JCam98/me210-engineering-design-graphics/Assignments/Reverse Engineering Project/Design Checks/Design_Check_4/PDFS/PART_1_PLASTIC_CASE.pdf

## PLASTIC CASE

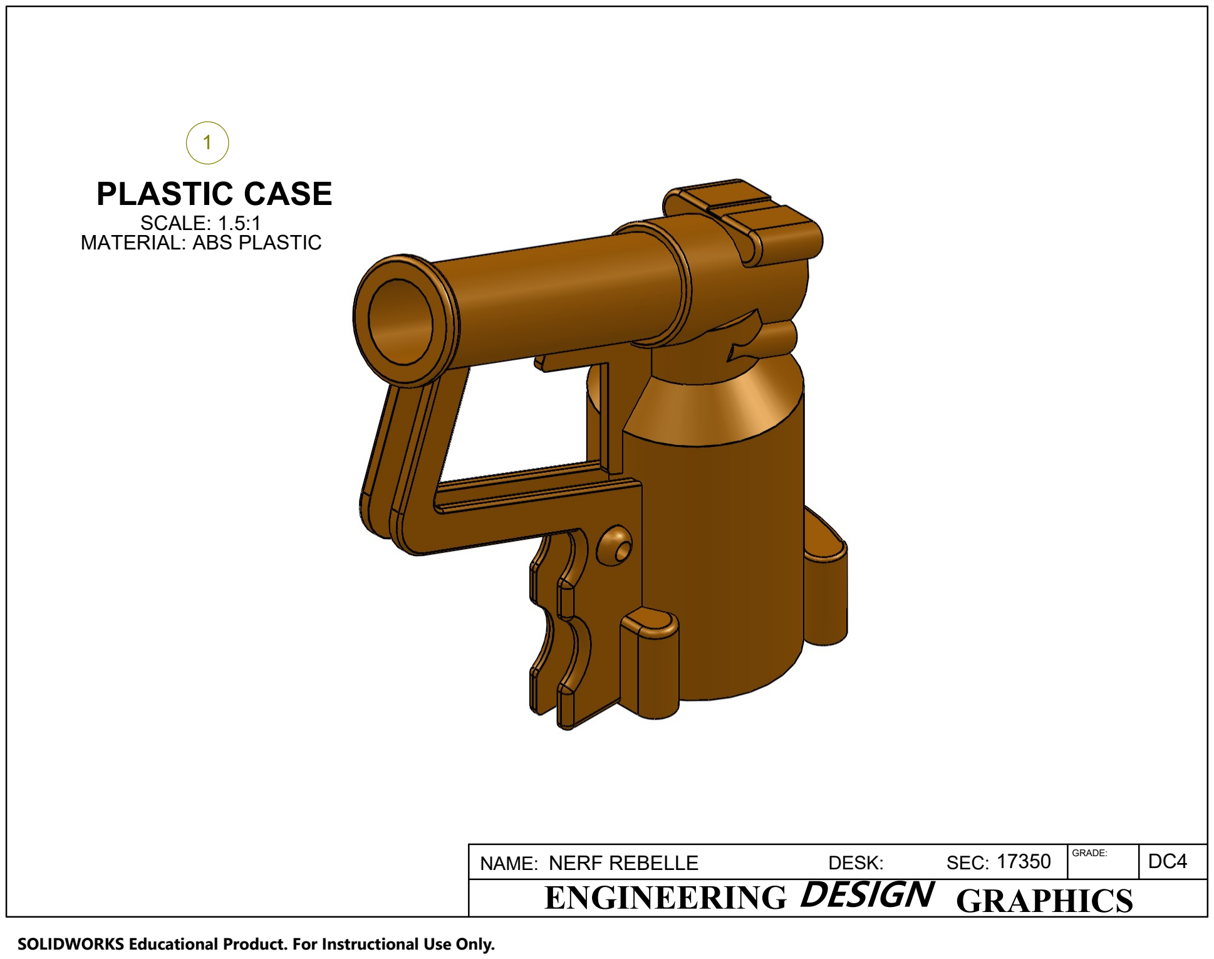
[picture p123: page 1]

# ENGINEERING DESIGN GRAPHICS

NAME: | DESK: | GRADE: SEC:

MATERIAL: ABS PLASTIC

17350

SCALE: 1.5:1

DC4

1

NERF REBELLE

SOLIDWORKS Educational Product. For Instructional Use Only.
