JCam98/me210-engineering-design-graphics/Assignments/Reverse Engineering Project/Design Checks/Design_Check_4/PDFS/PART_3_PHILLIPS_SCREW.pdf

## PHILLIP'S SCREW

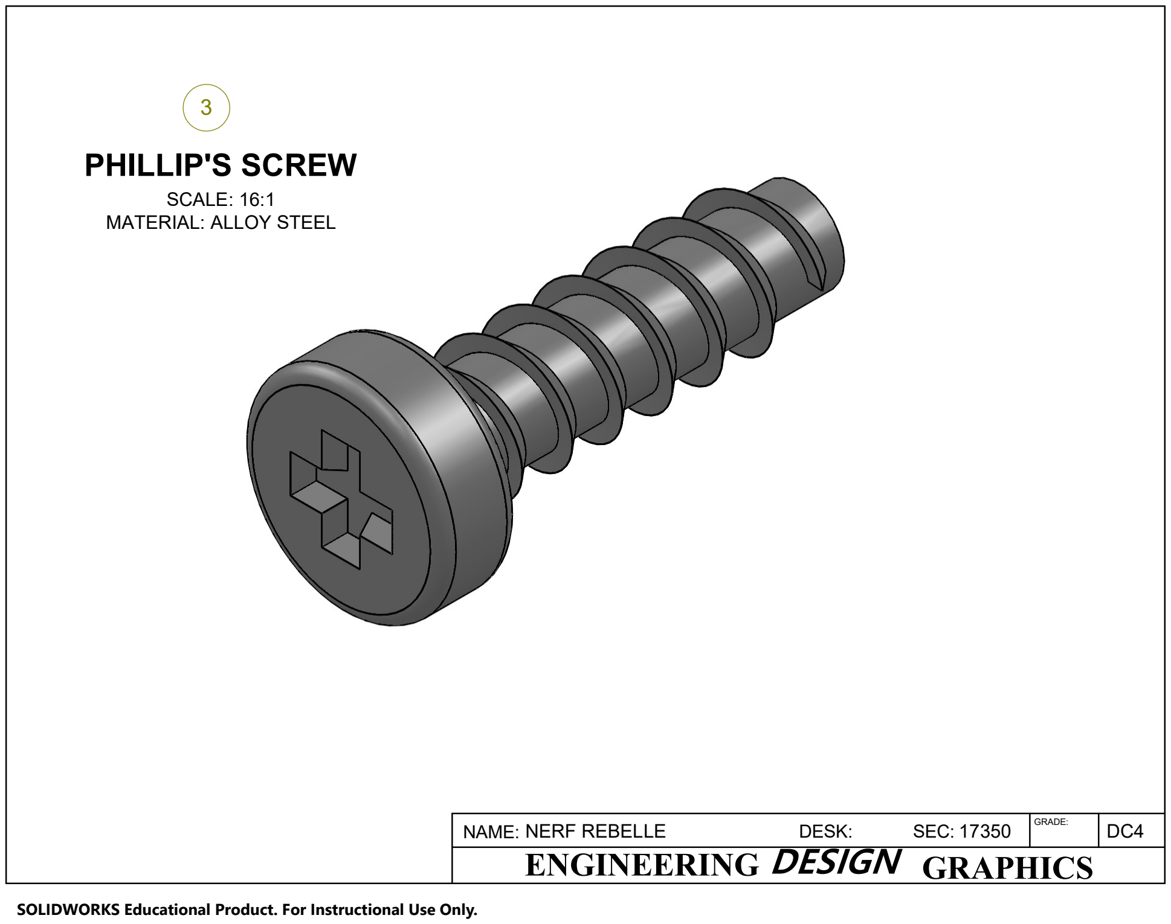
[picture p124: page 1]

# ENGINEERING DESIGN GRAPHICS

NAME: | DESK: | GRADE: SEC:

3

NERF REBELLE | 17350

MATERIAL: ALLOY STEEL

SCALE: 16:1

DC4

SOLIDWORKS Educational Product. For Instructional Use Only.
