JCam98/me210-engineering-design-graphics/Assignments/Reverse Engineering Project/Design Checks/Design_Check_4/PDFS/Shaft_Head_Rivet.pdf

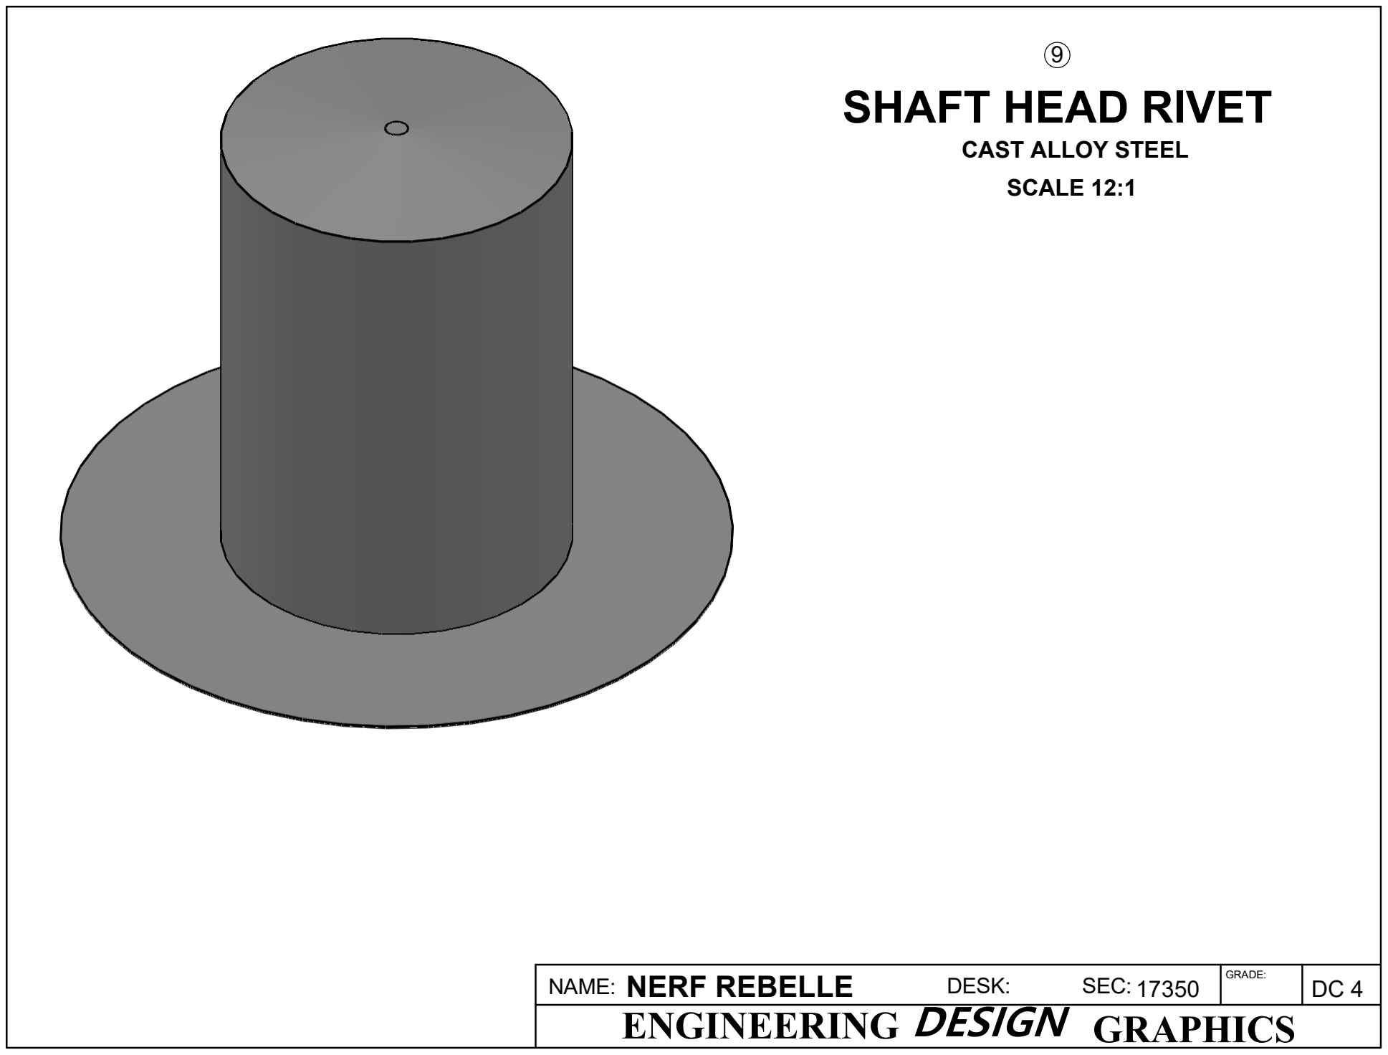
[picture p125: page 1]

DESK: | GRADE:
D E S I G N ENGINEERING | GRAPHICS
NAME: | SEC:

SCALE 12:1

NERF REBELLE | 17350

SHAFT HEAD RIVET

CAST ALLOY STEEL

9

DC 4
