JCam98/me210-engineering-design-graphics/Assignments/Reverse Engineering Project/Design Checks/Design_Check_6/200N_displacement_plot1.pdf

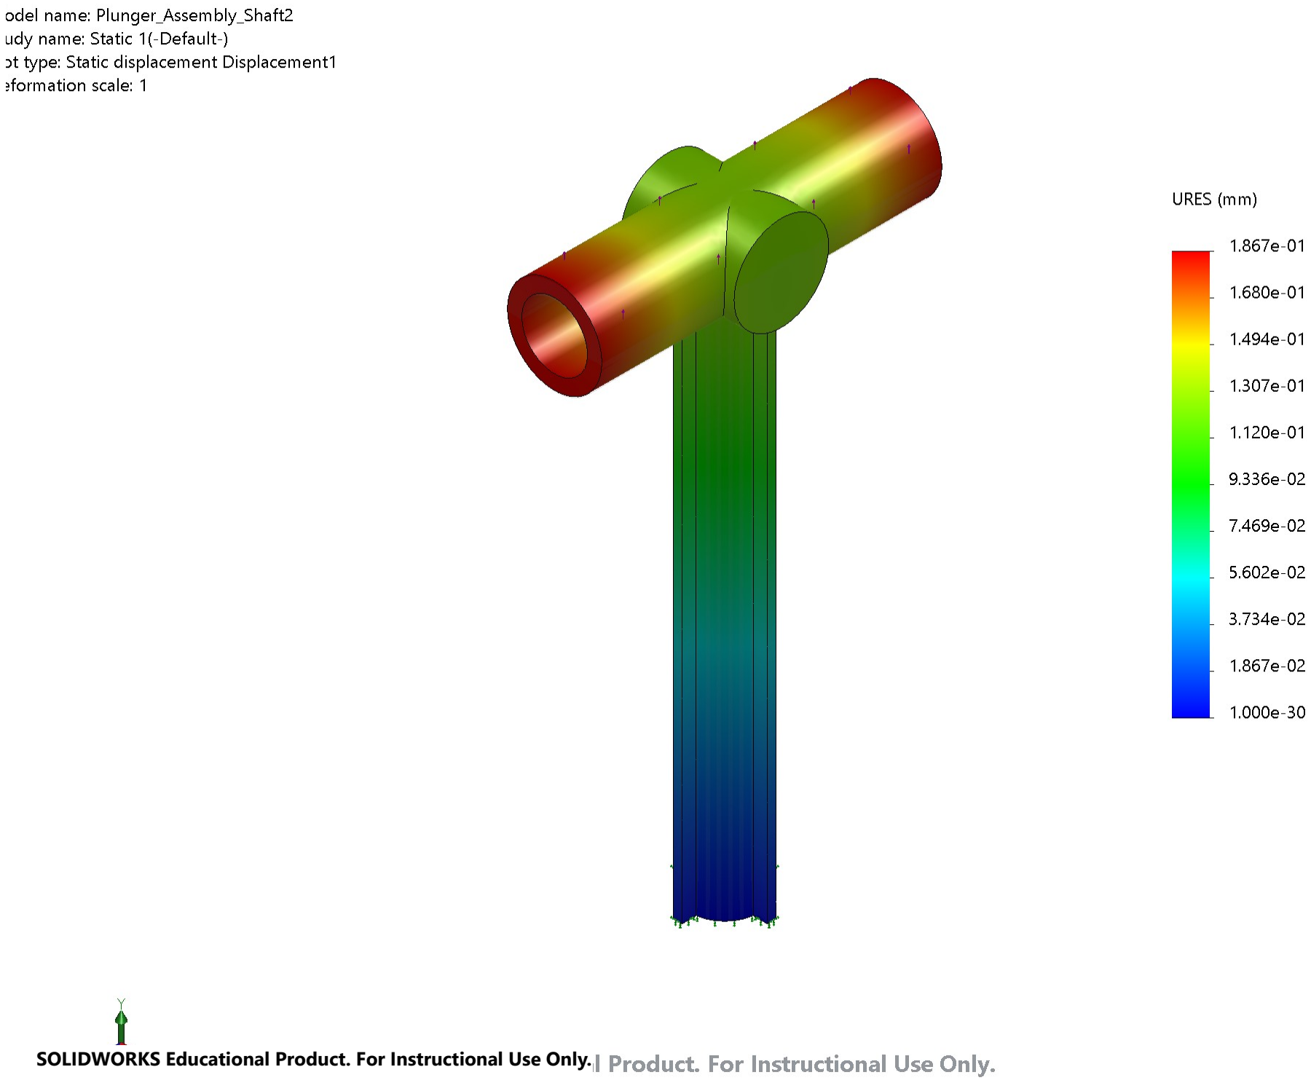
[picture p132: page 1]

SOLIDWORKS Educational Product. For Instructional Use Only.
