JCam98/me210-engineering-design-graphics/Assignments/Reverse Engineering Project/Design Checks/Design_Check_6/300N_stress_plot_1.pdf

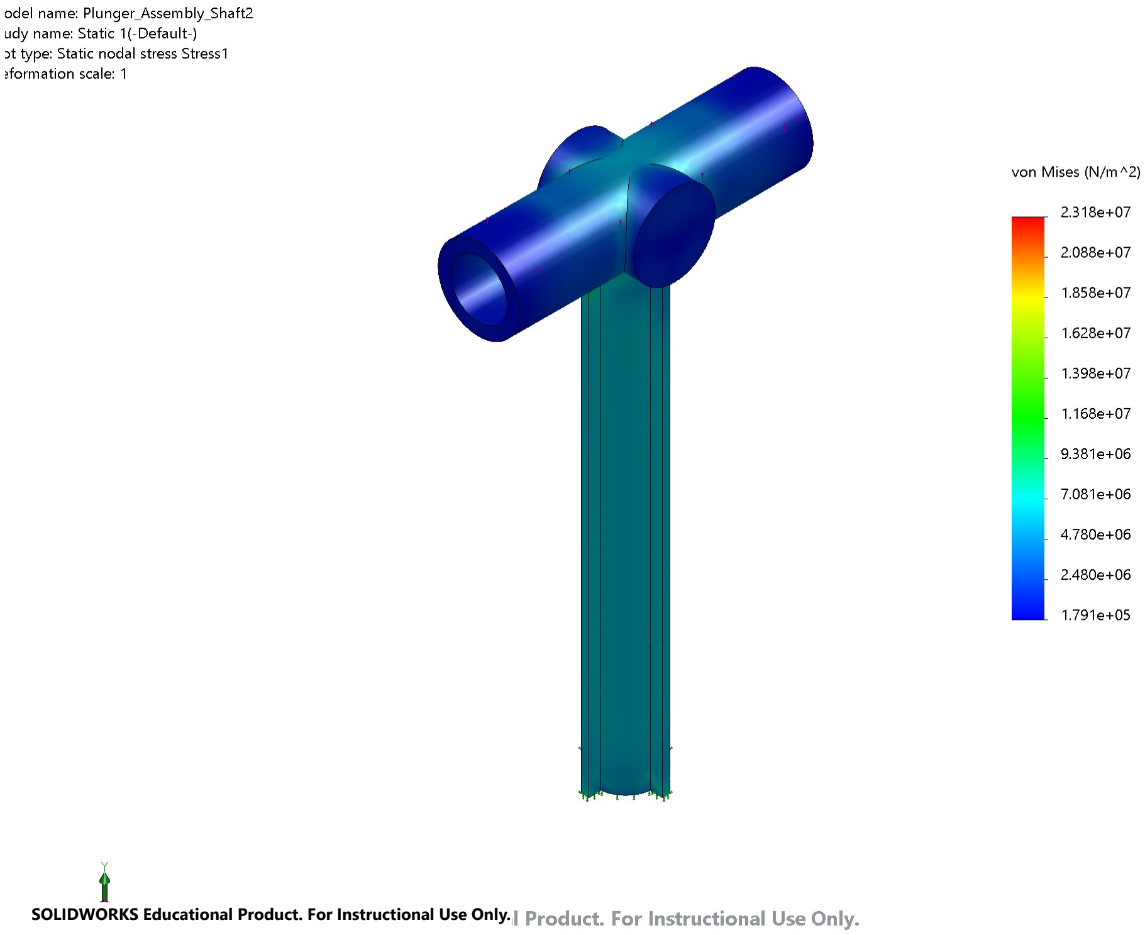
[picture p137: page 1]

SOLIDWORKS Educational Product. For Instructional Use Only.
