JCam98/me210-engineering-design-graphics/Assignments/Reverse Engineering Project/Design Checks/Design_Check_6/75N_strain_1_plot.pdf

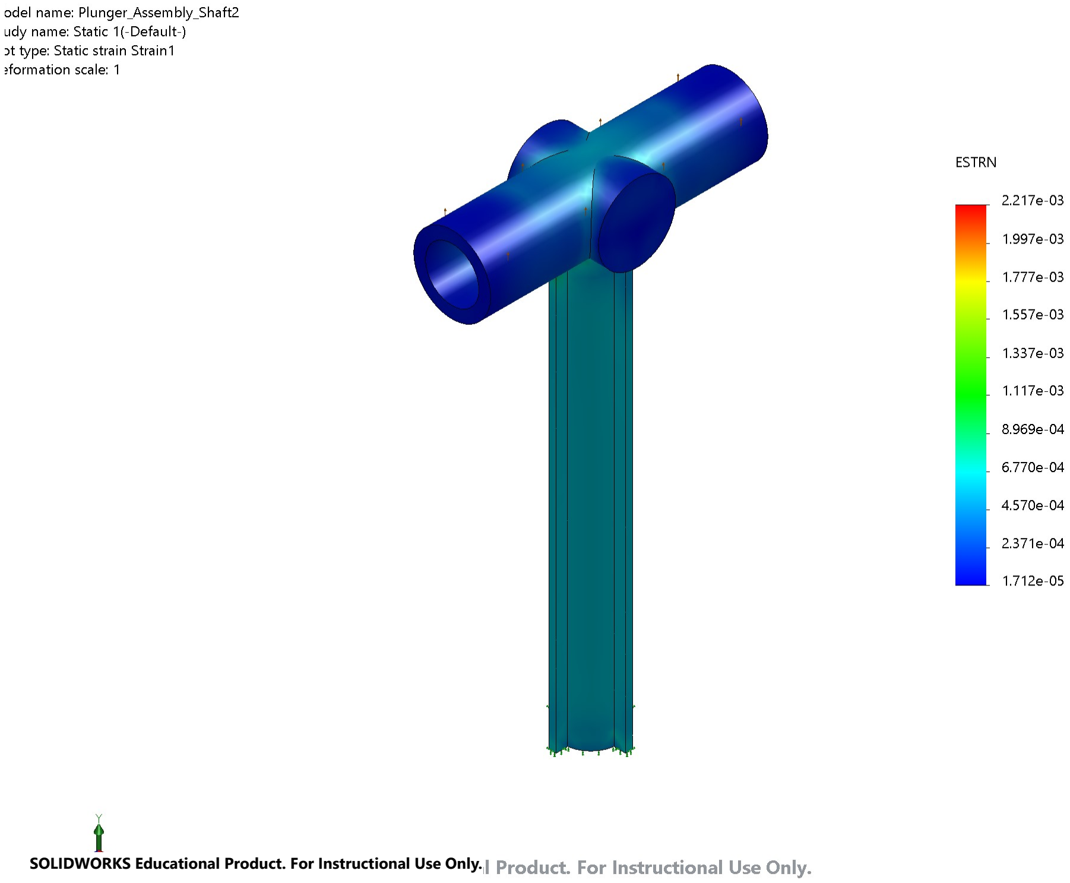
[picture p139: page 1]

SOLIDWORKS Educational Product. For Instructional Use Only.
