JCam98/me210-engineering-design-graphics/Assignments/Sketches - Exercisees/Sketch 1.1.pdf

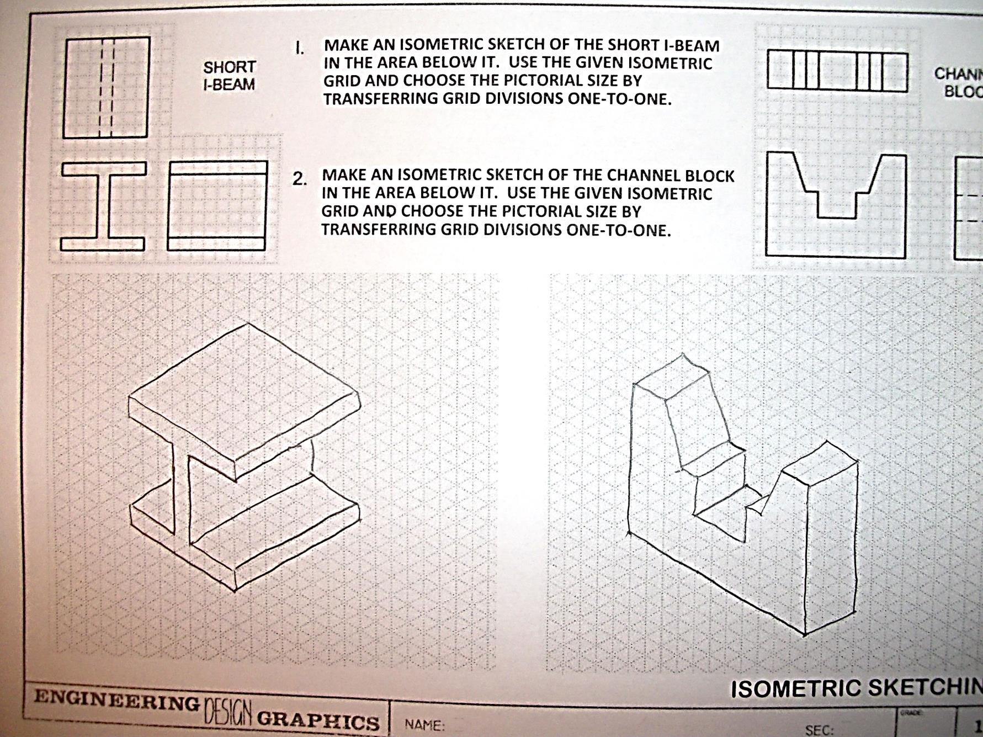
[picture p141: page 1]
