JCam98/me210-engineering-design-graphics/Assignments/Sketches - Exercisees/Sketch 1.3.pdf

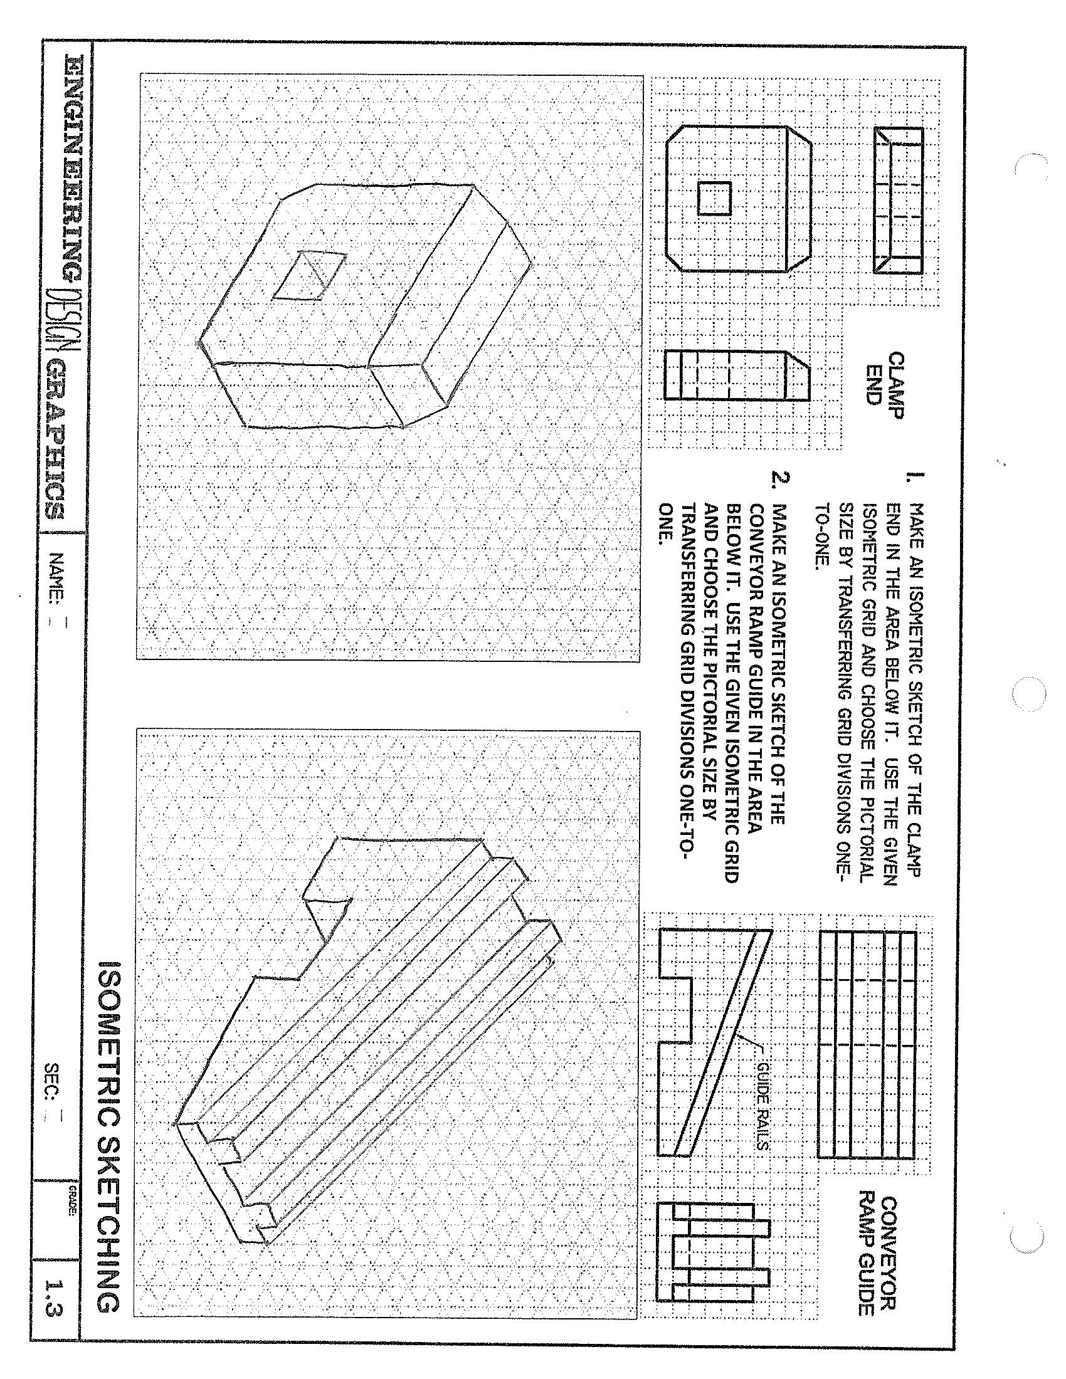
[picture p142: page 1]
