JCam98/me210-engineering-design-graphics/Assignments/Sketches - Exercisees/Sketch 1.4 - Correction.pdf

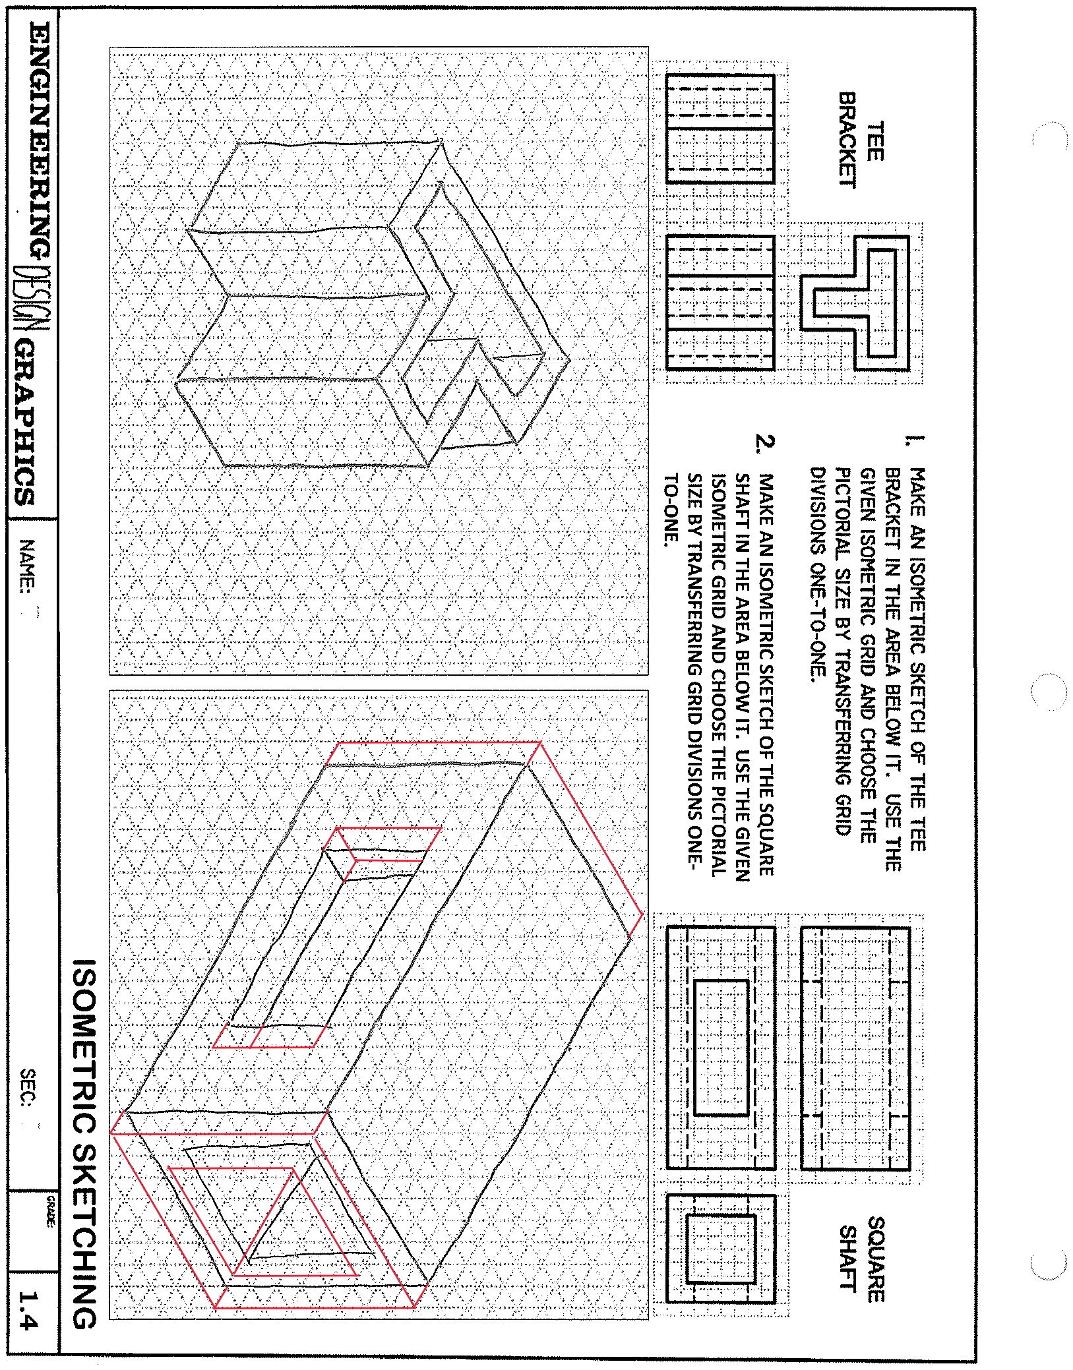
[picture p143: page 1]
