JCam98/me210-engineering-design-graphics/Assignments/Sketches - Exercisees/Sketch 1.5.pdf

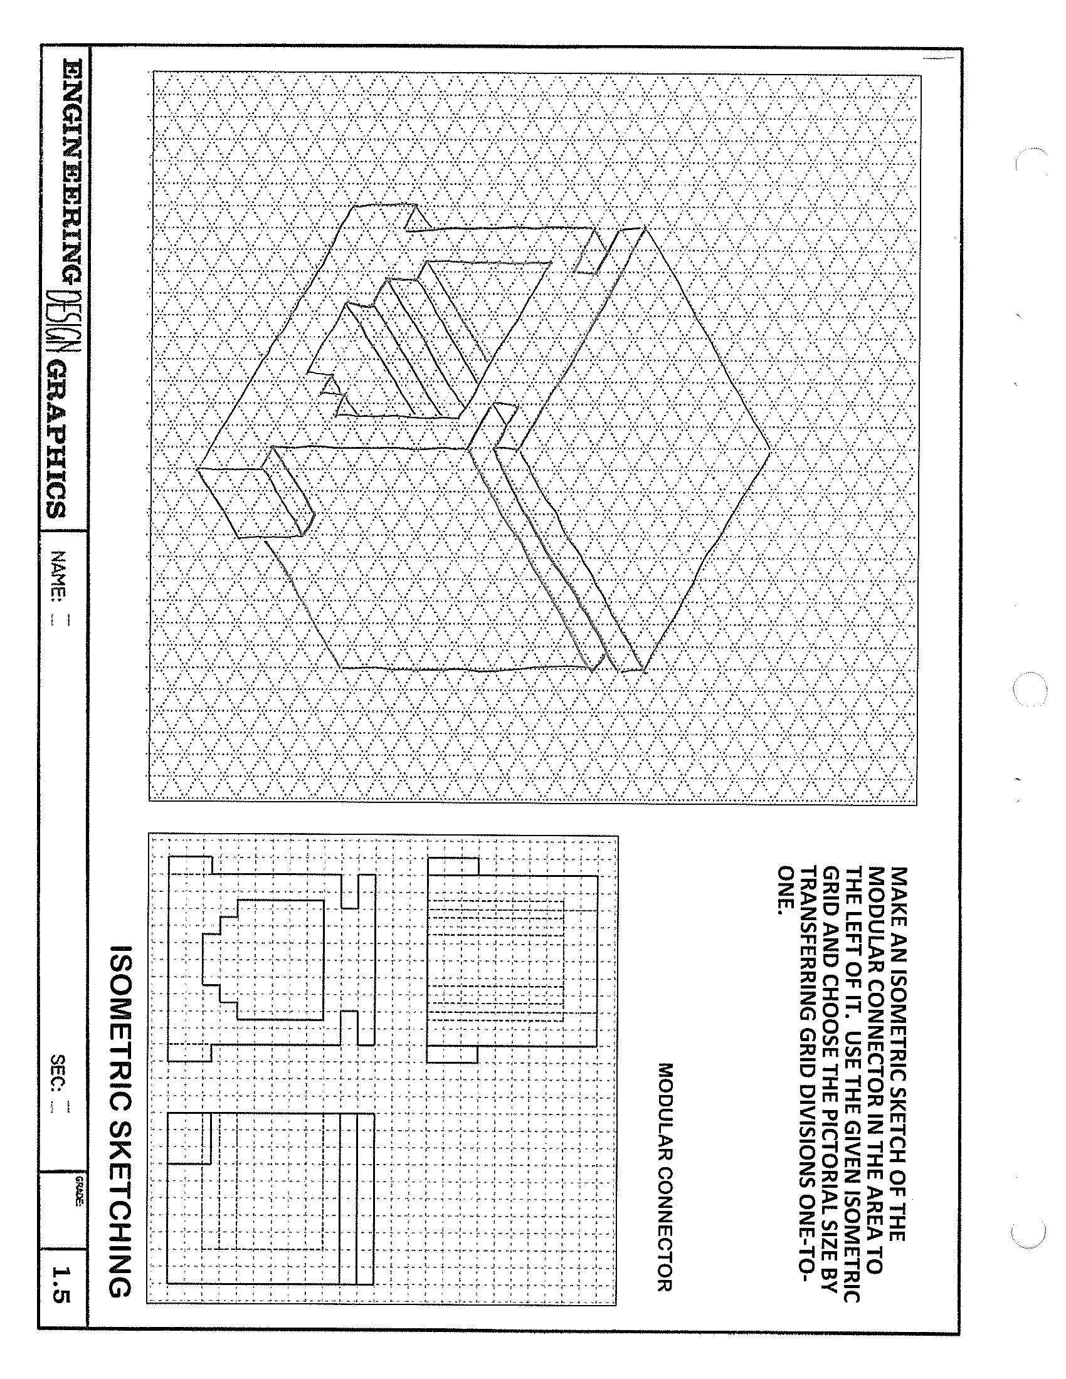
[picture p144: page 1]
