JCam98/me210-engineering-design-graphics/Assignments/Sketches - Exercisees/Sketch 2.1.pdf

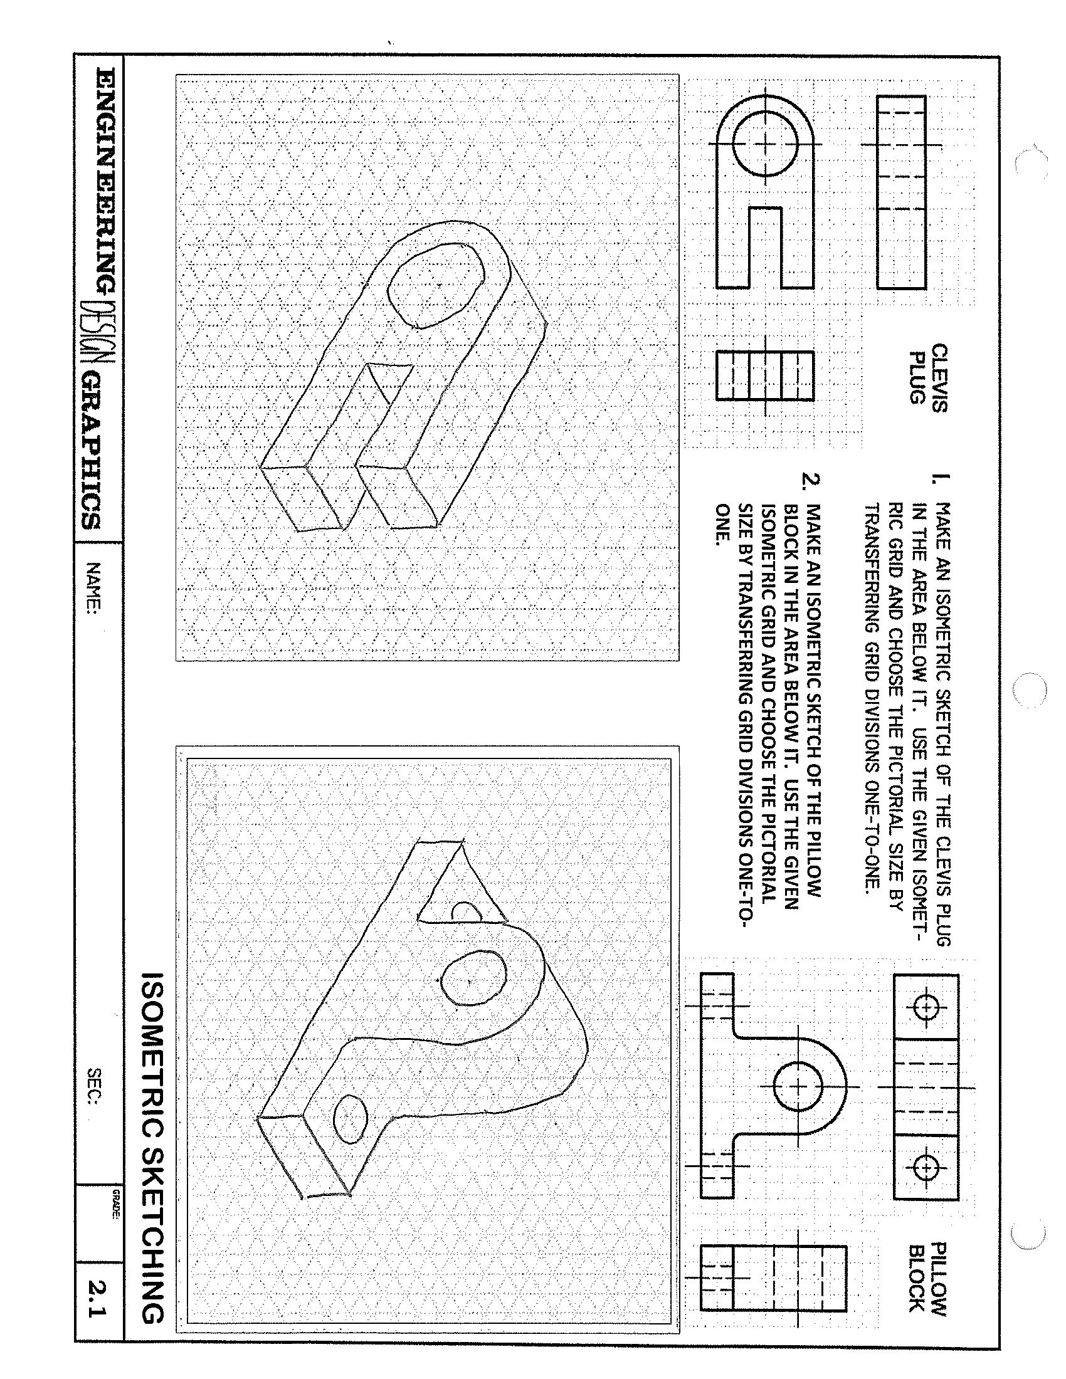
[picture p145: page 1]
