JCam98/me210-engineering-design-graphics/Assignments/Sketches - Exercisees/Sketch 2.2.pdf

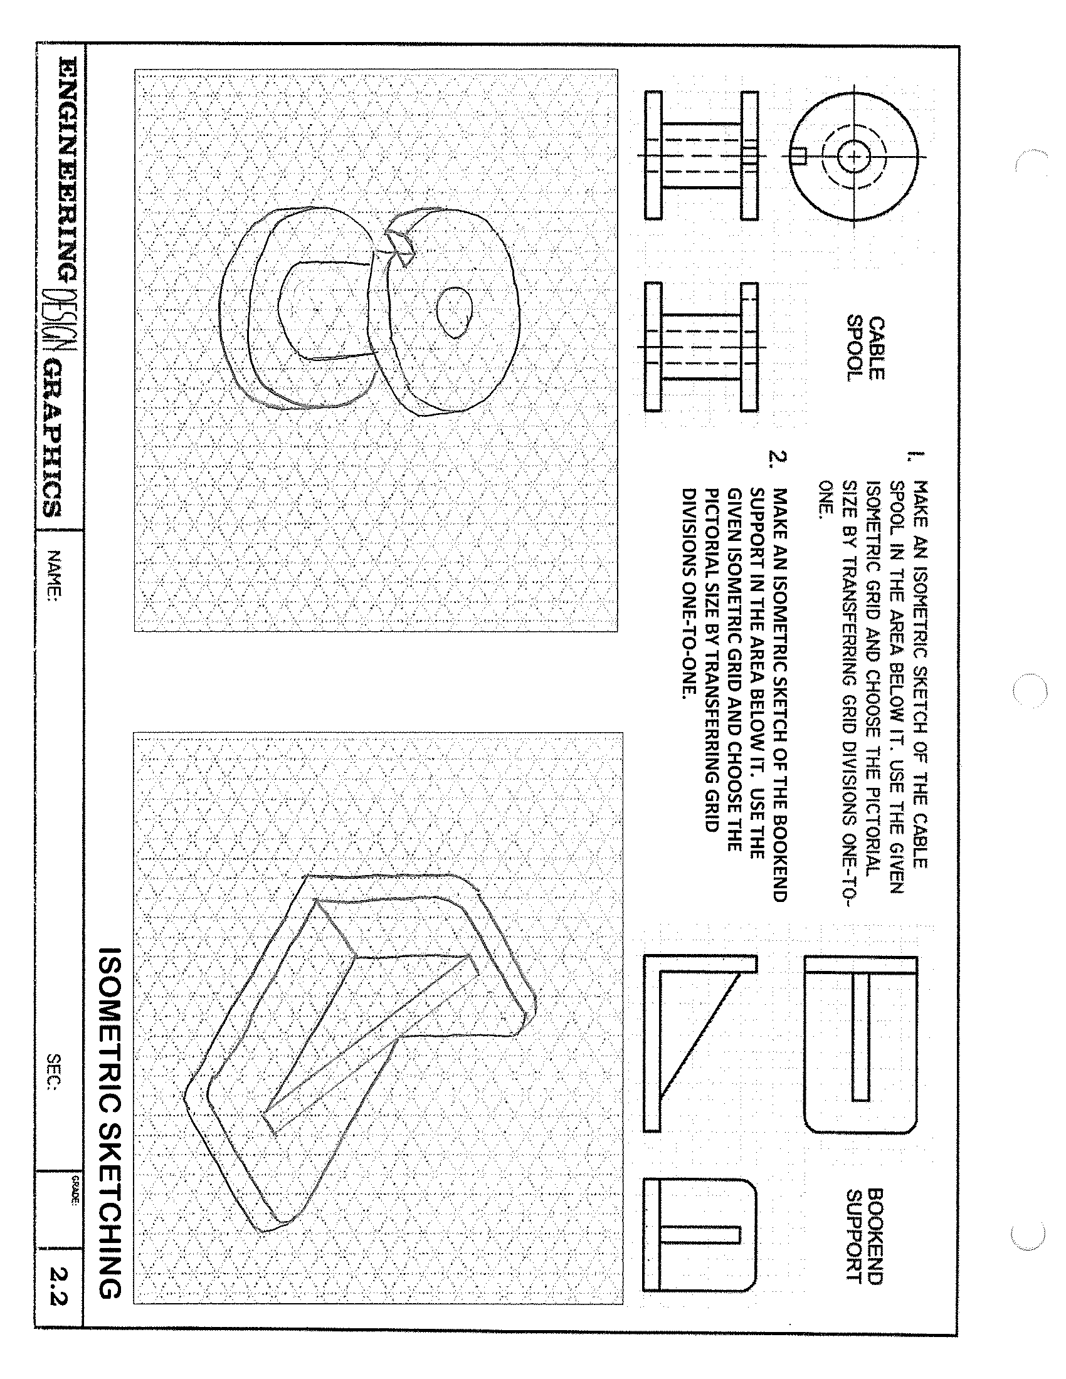
[picture p146: page 1]
