JCam98/me210-engineering-design-graphics/Assignments/Sketches - Exercisees/Sketch 2.3.pdf

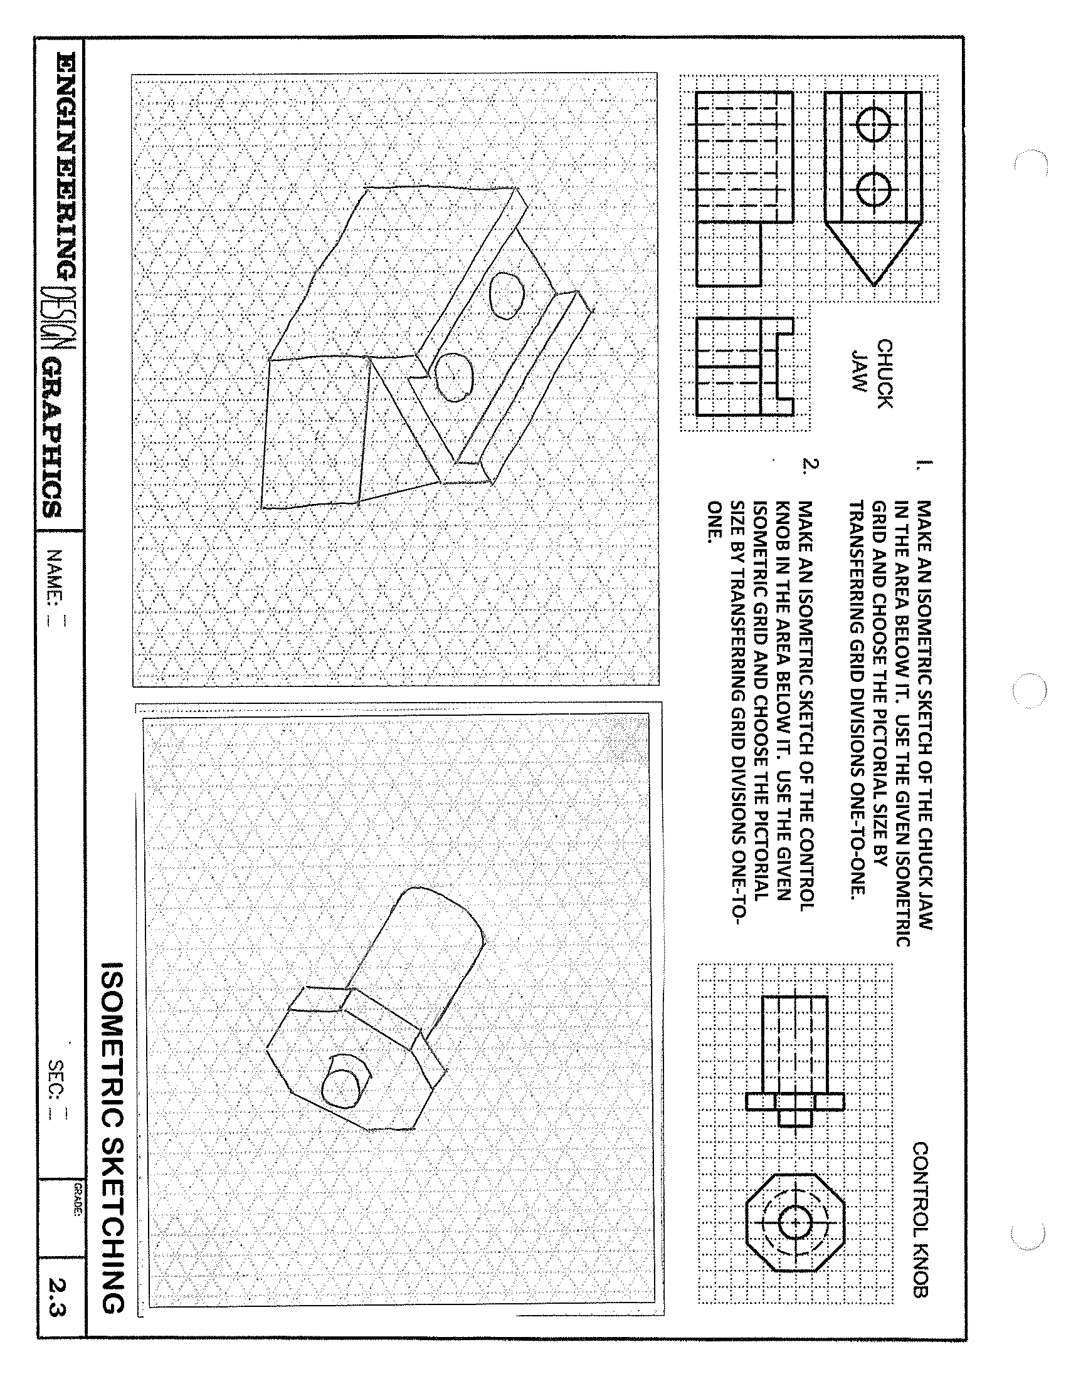
[picture p147: page 1]
