JCam98/me210-engineering-design-graphics/Assignments/Sketches - Exercisees/Sketch 2.4 tangent correction.pdf

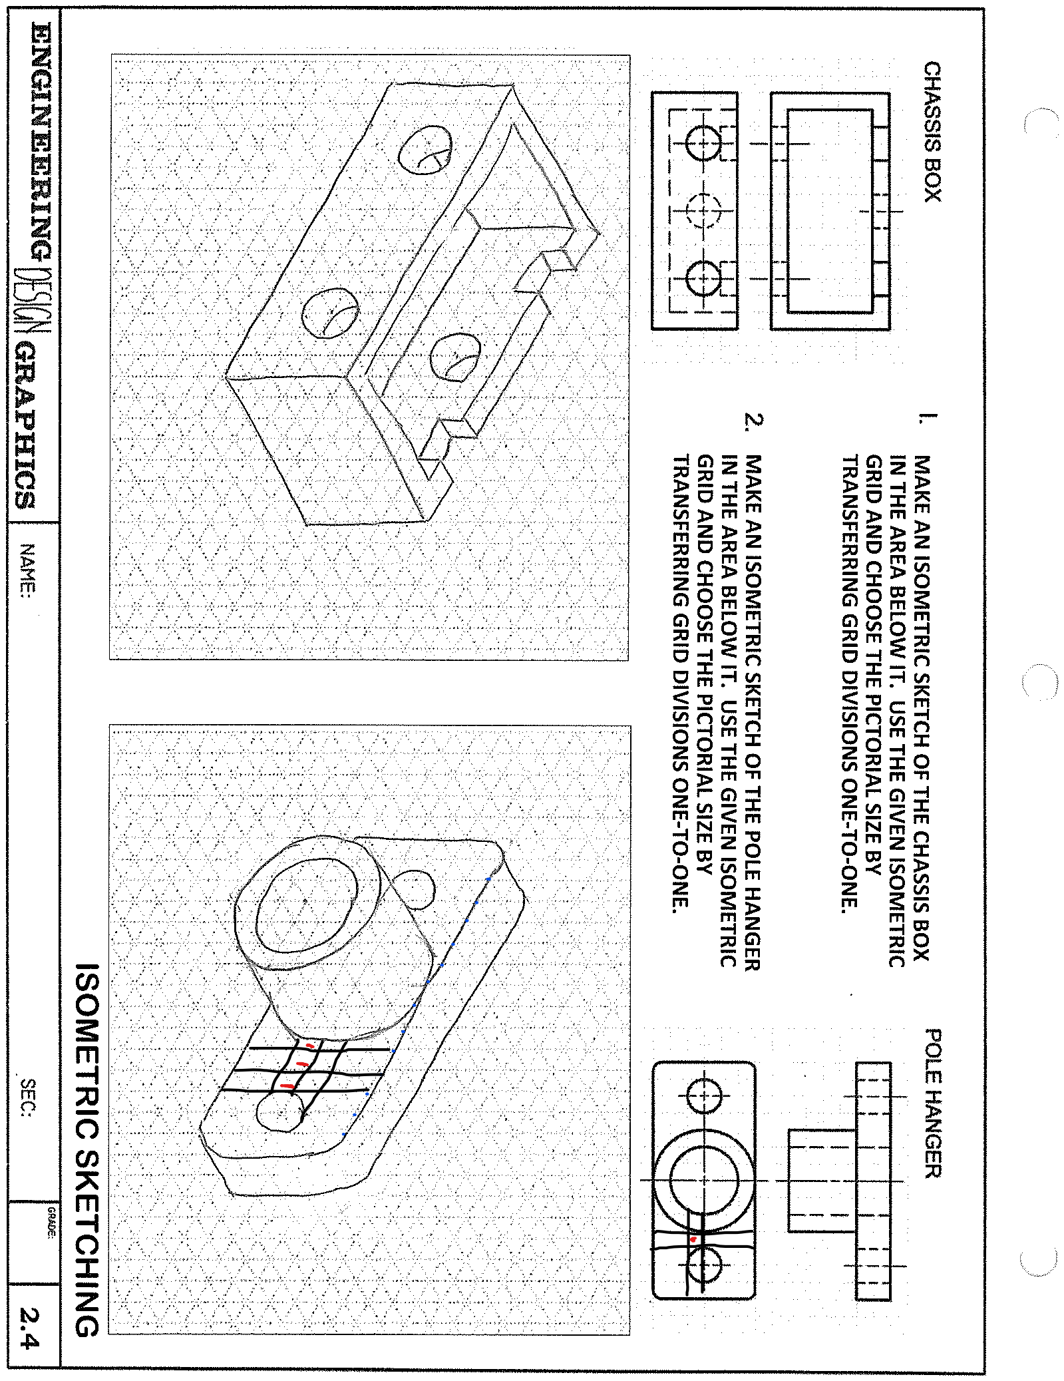
[picture p148: page 1]
