JCam98/me210-engineering-design-graphics/Assignments/Sketches - Exercisees/Sketch 2.5.pdf

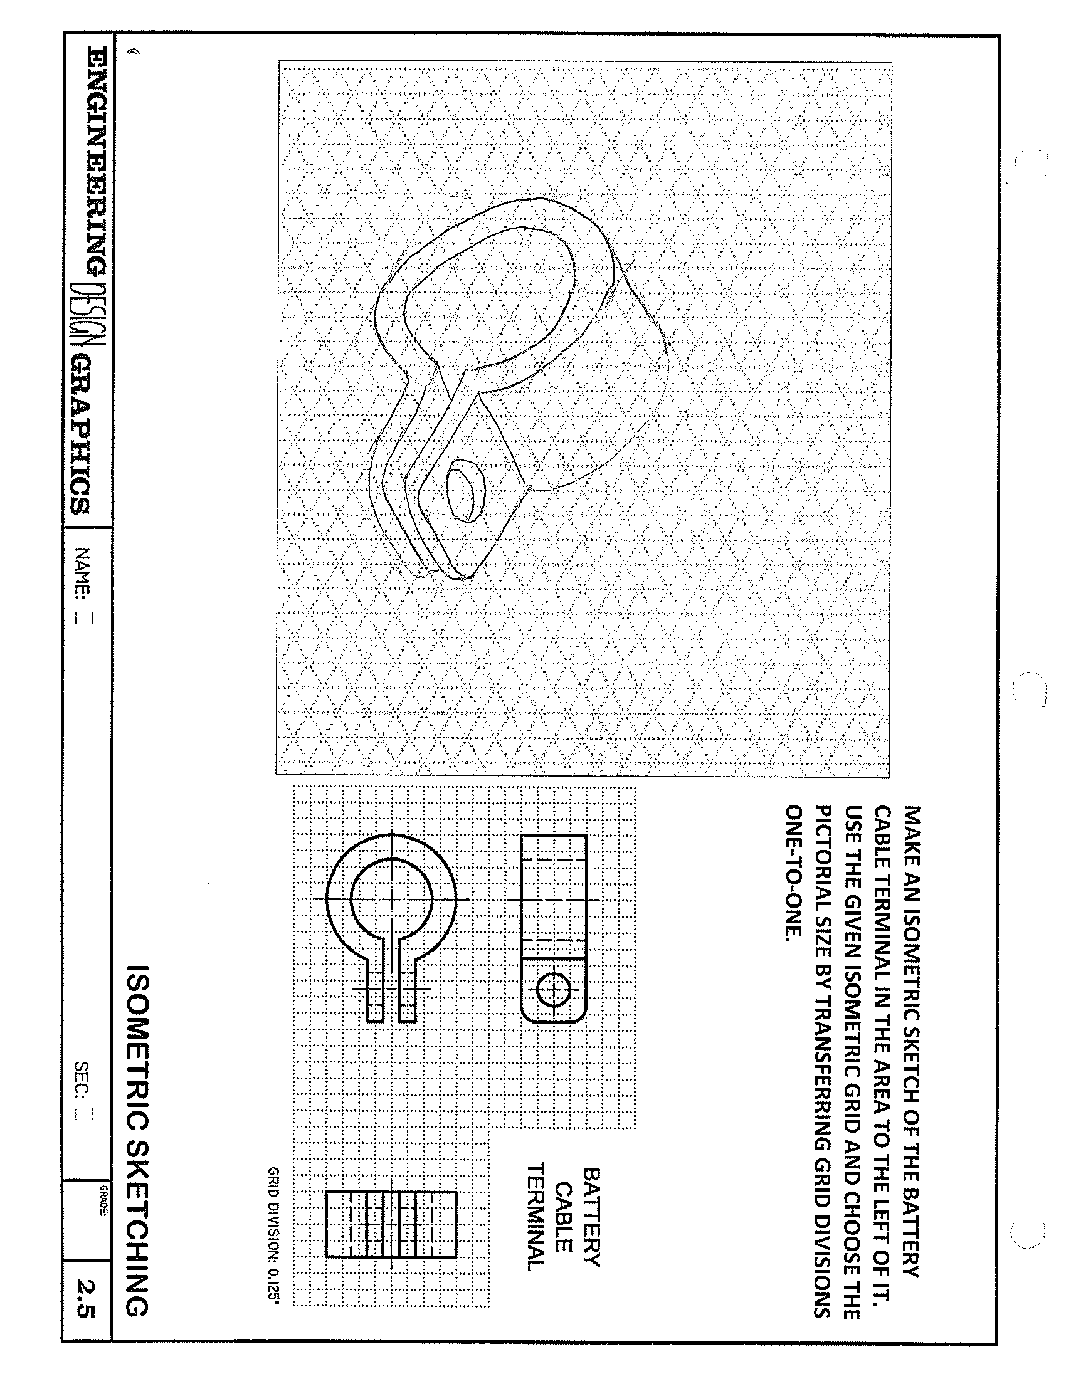
[picture p149: page 1]
