JCam98/me210-engineering-design-graphics/Assignments/Sketches - Exercisees/Sketch 3.1.pdf

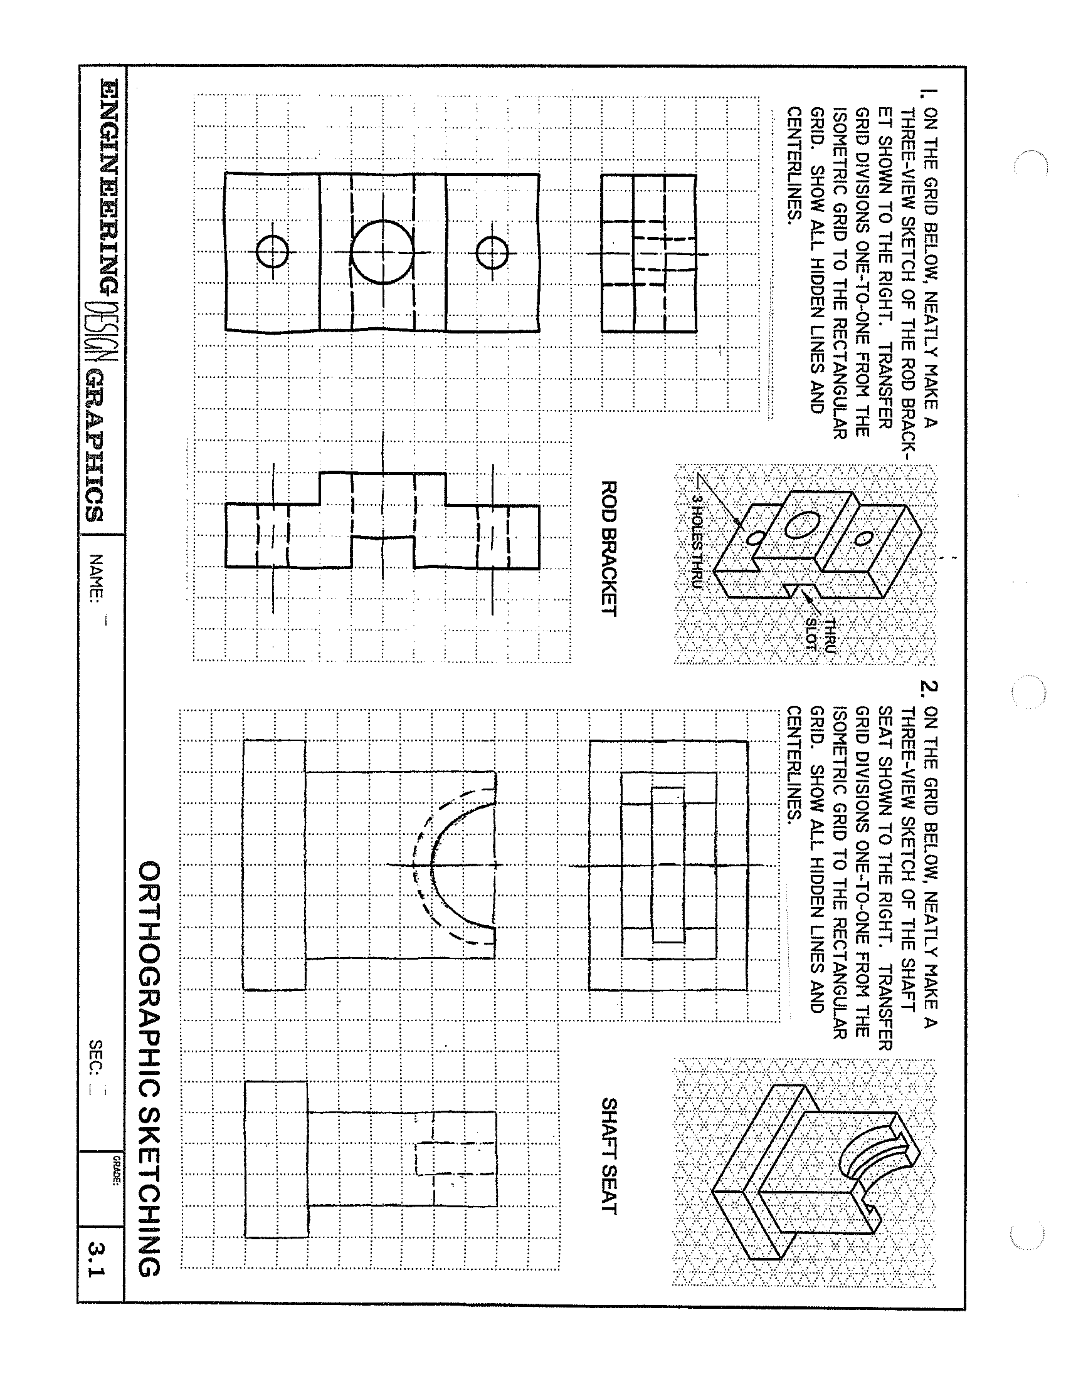
[picture p150: page 1]
