JCam98/me210-engineering-design-graphics/Assignments/Sketches - Exercisees/Sketch 3.2.pdf

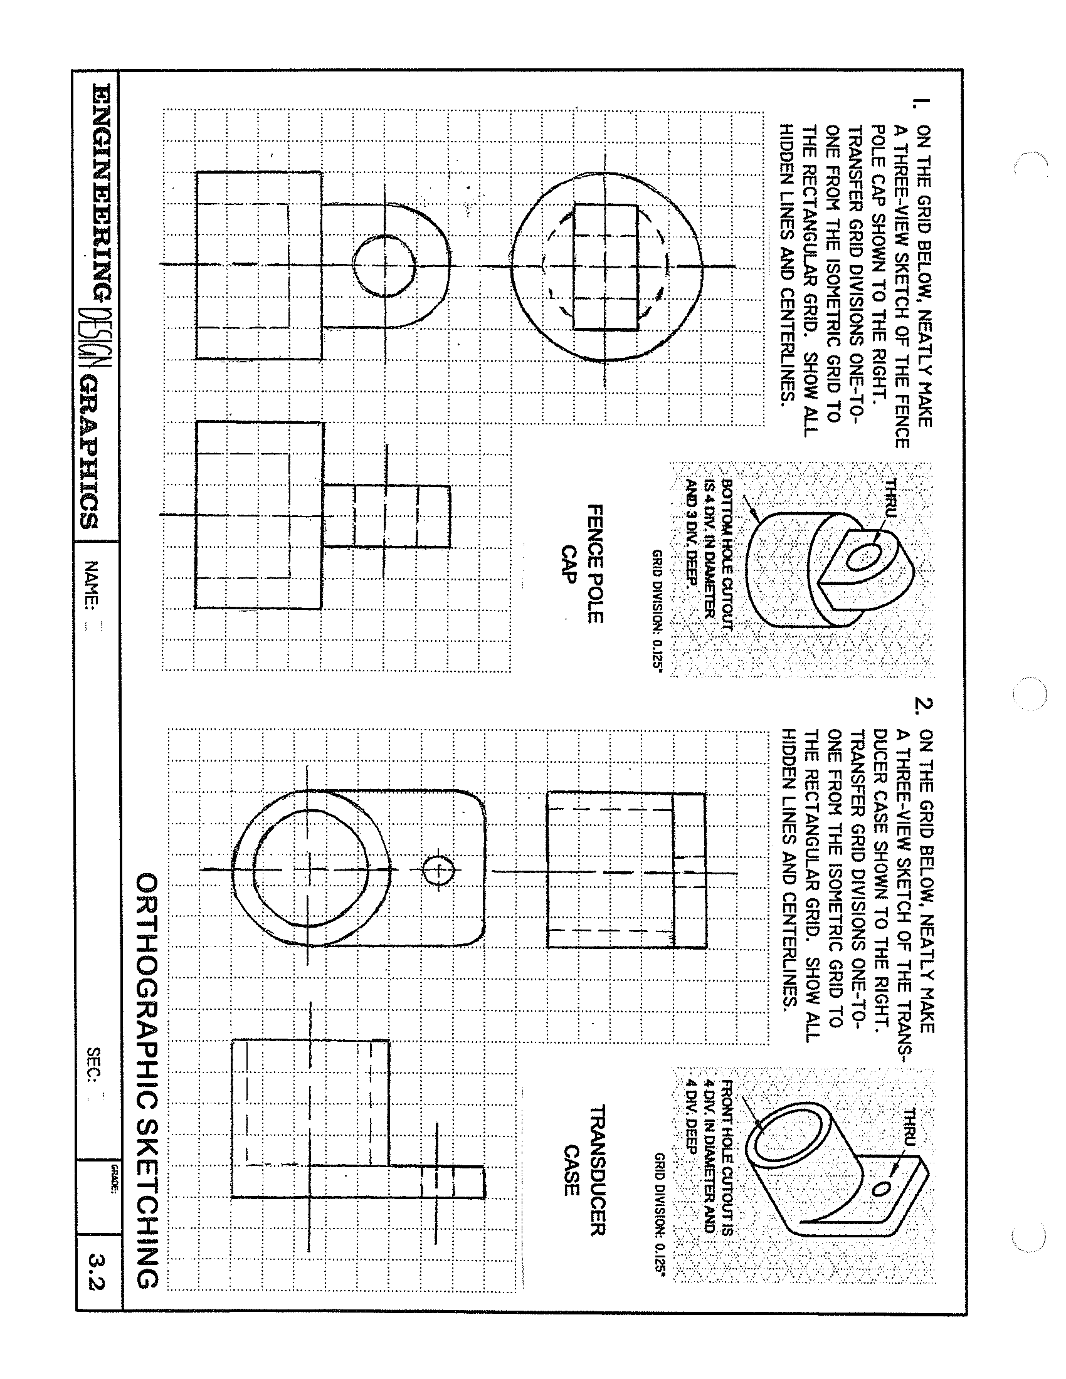
[picture p151: page 1]
