JCam98/me210-engineering-design-graphics/Assignments/Sketches - Exercisees/Sketch 3.3.pdf

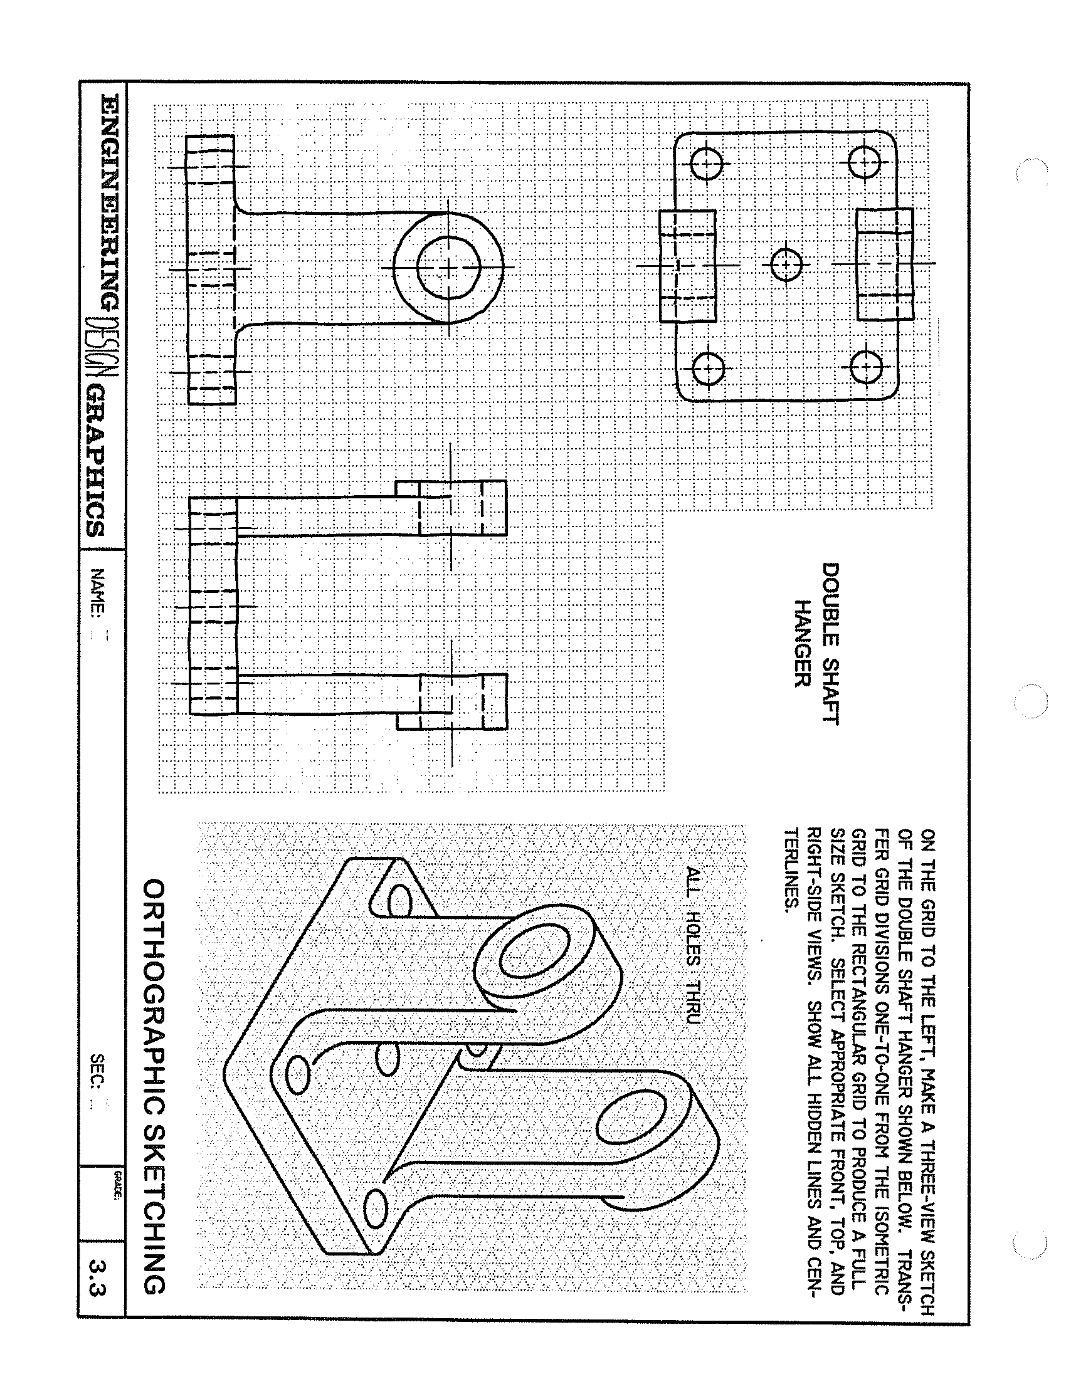
[picture p152: page 1]
