JCam98/me210-engineering-design-graphics/Assignments/Sketches - Exercisees/Sketch 3.4.pdf

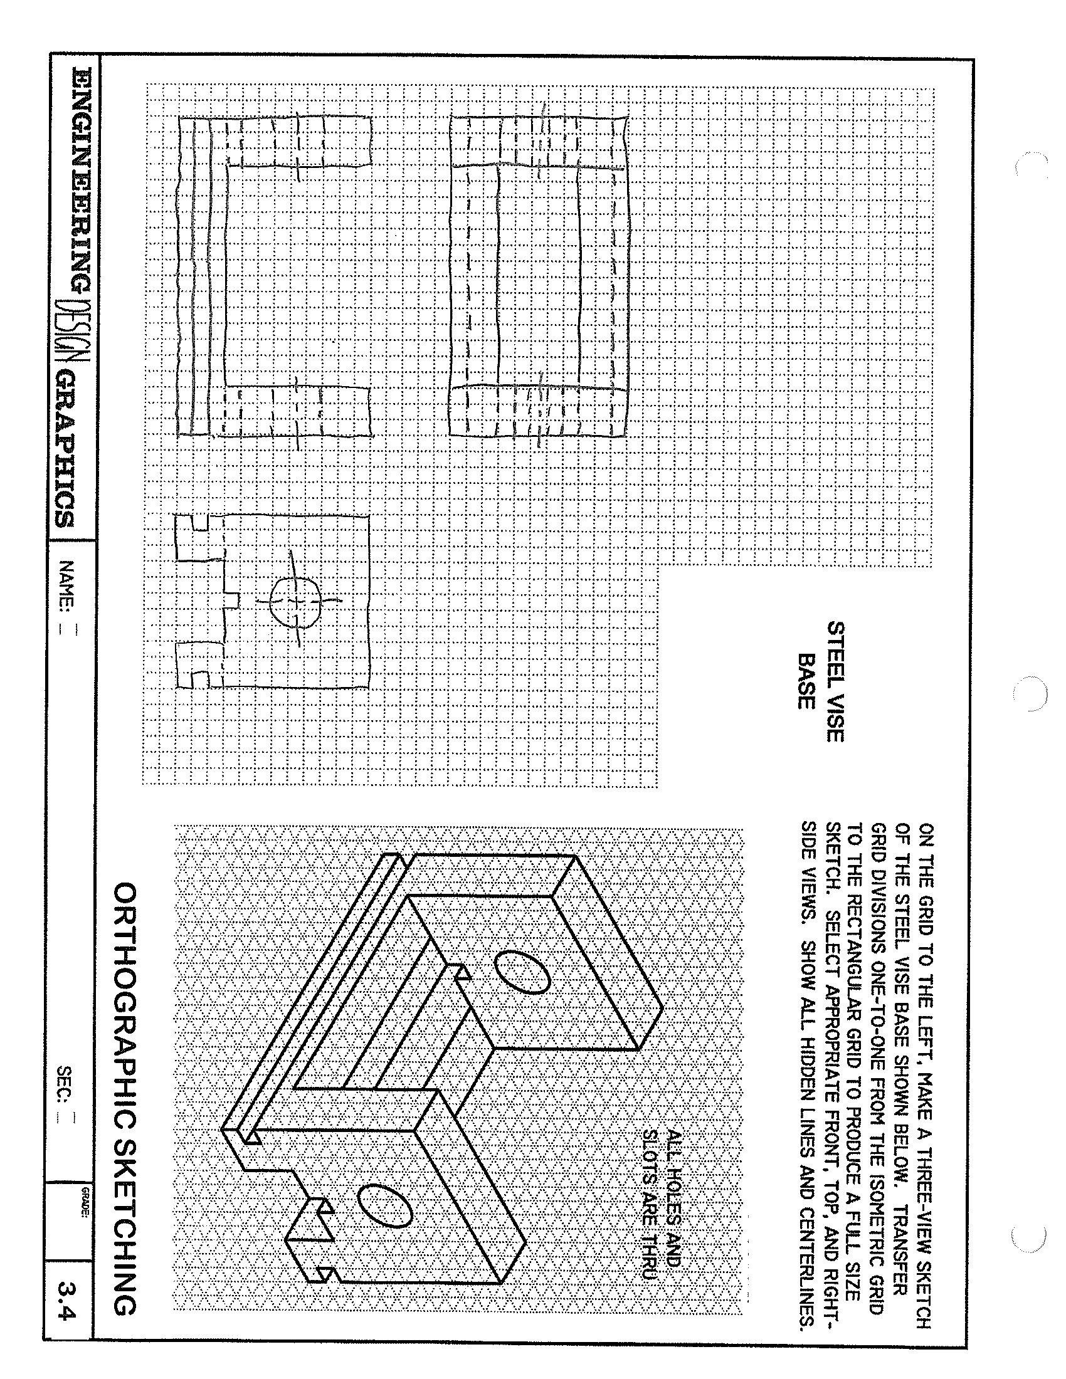
[picture p153: page 1]
