JCam98/me210-engineering-design-graphics/Assignments/Sketches - Exercisees/Sketch 3.5.pdf

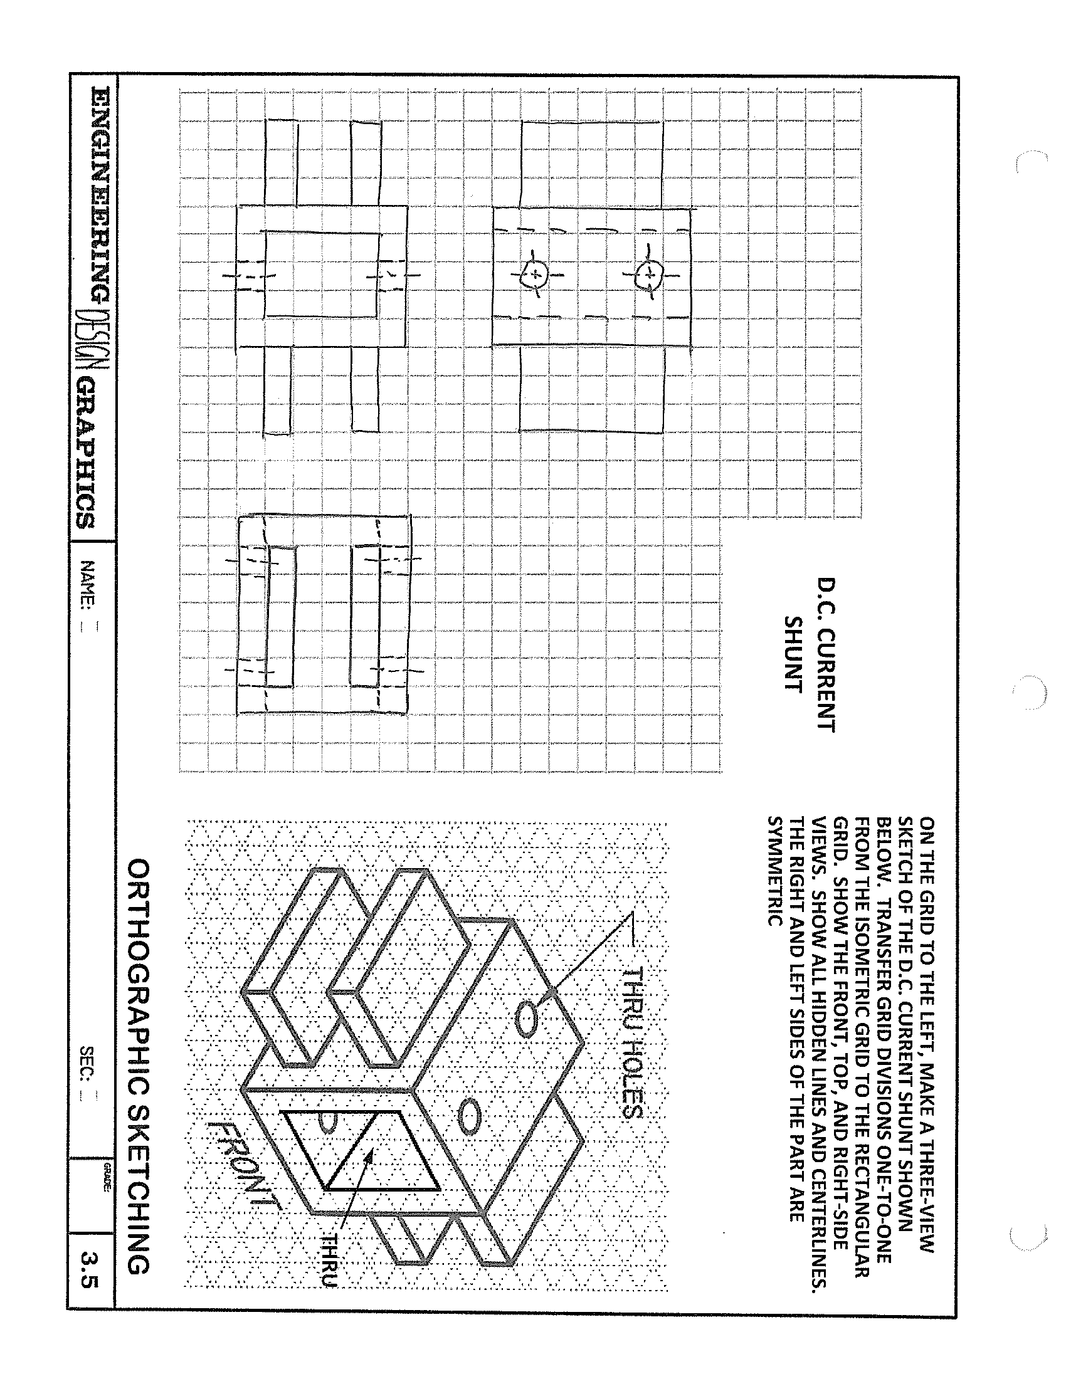
[picture p154: page 1]
