JCam98/me210-engineering-design-graphics/Assignments/Sketches - Exercisees/Sketch 4.1.pdf

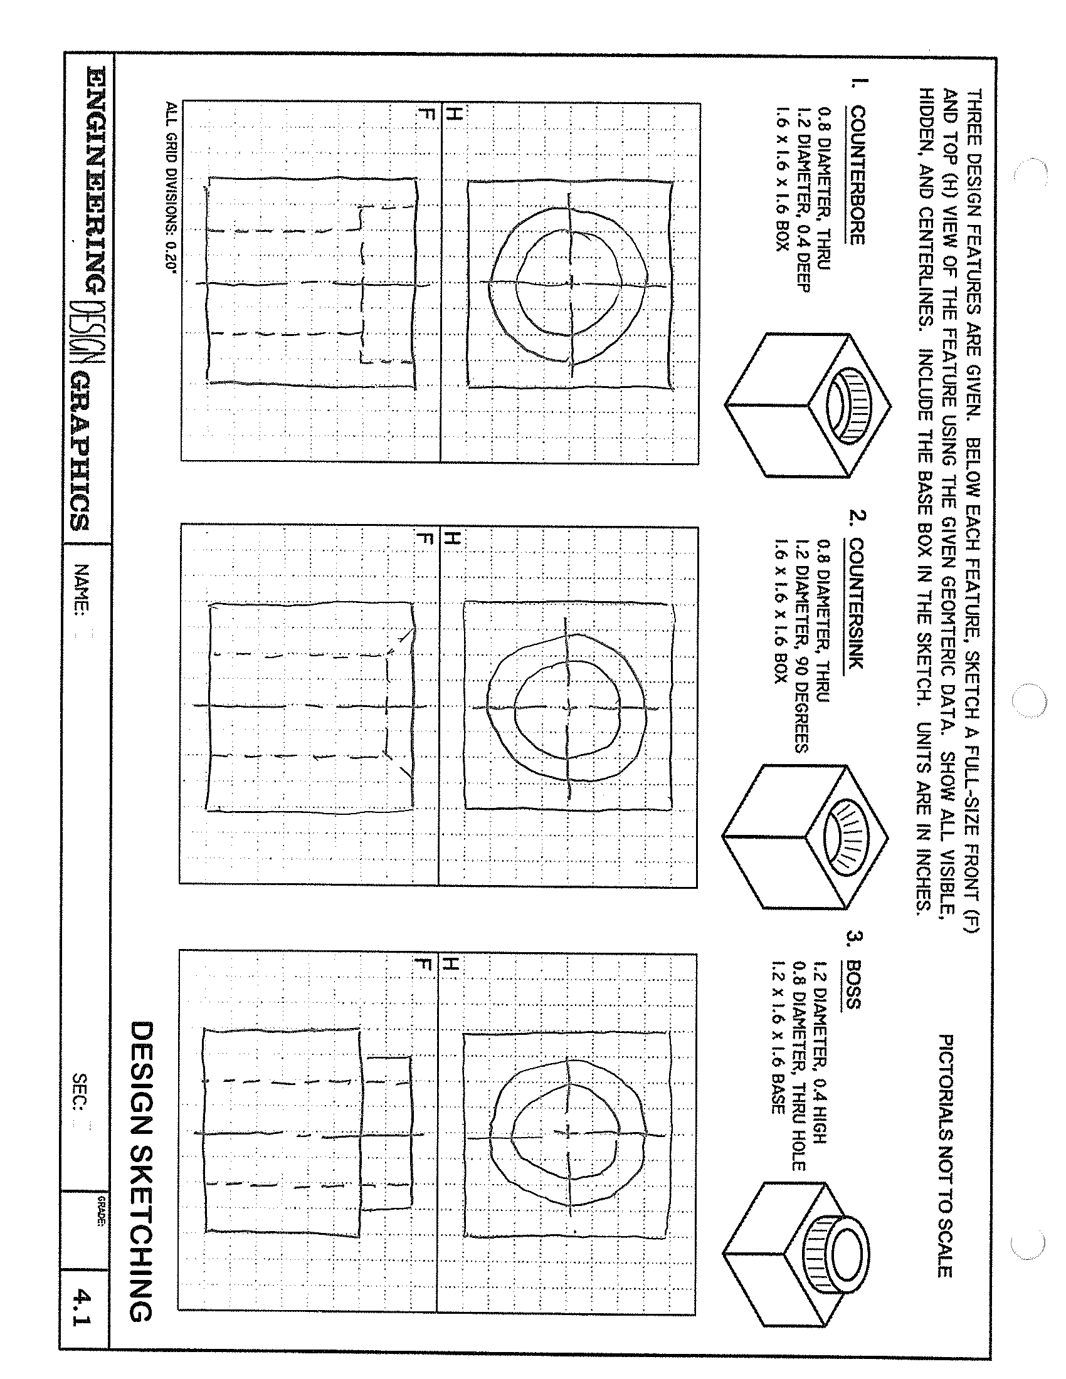
[picture p155: page 1]
