JCam98/me210-engineering-design-graphics/Assignments/Sketches - Exercisees/Sketch 4.2.pdf

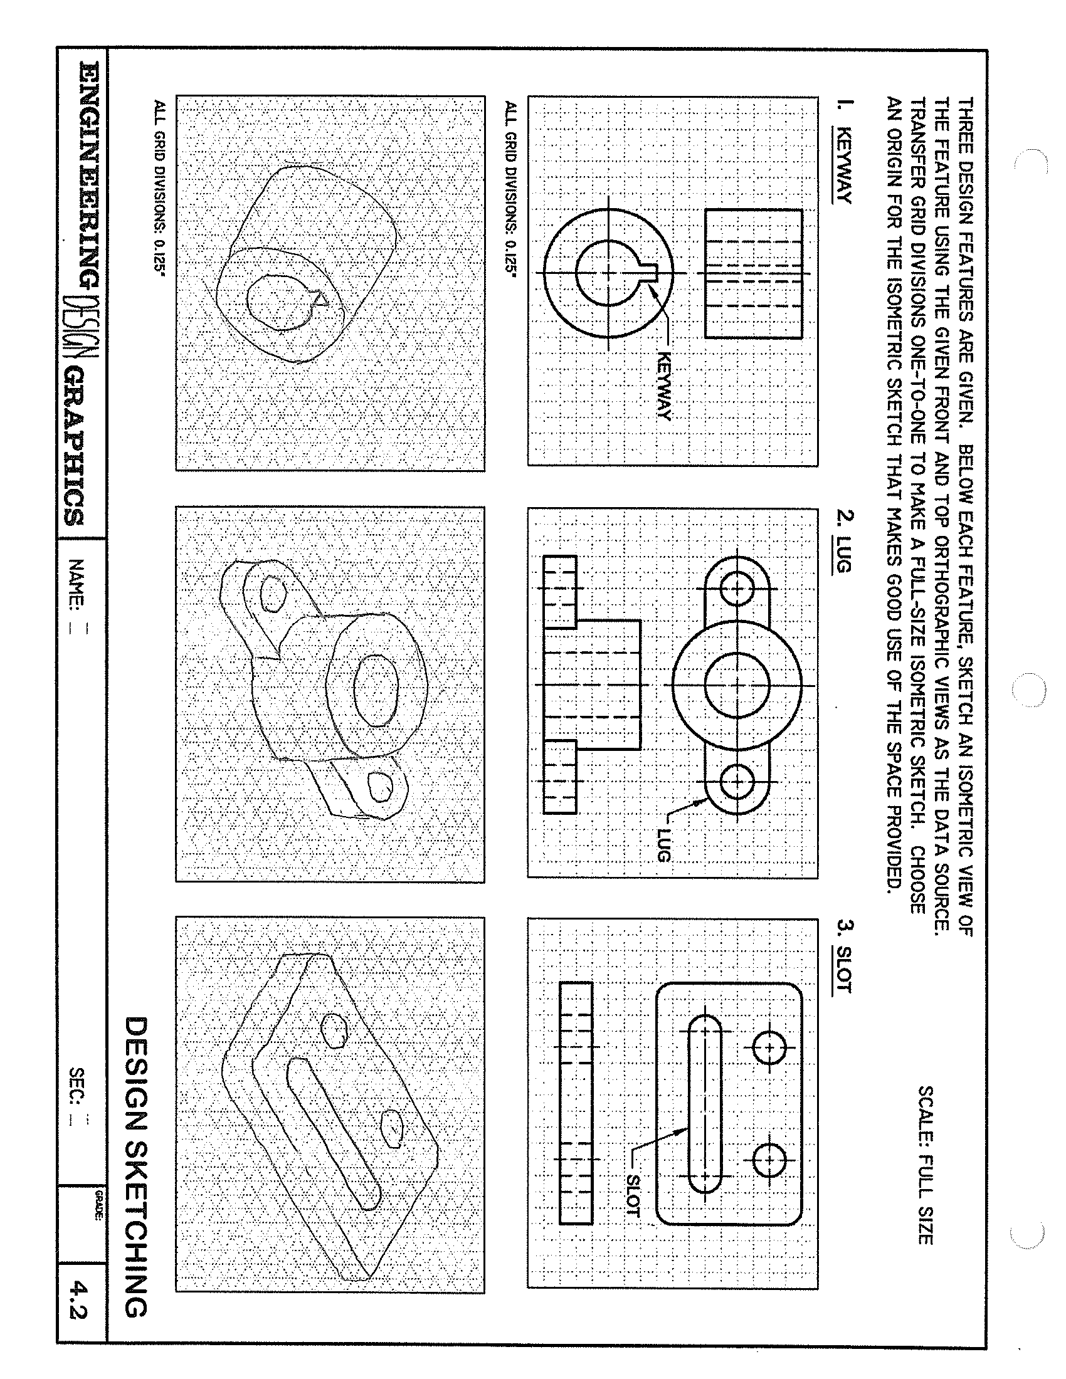
[picture p156: page 1]
