JCam98/me210-engineering-design-graphics/Assignments/Sketches - Exercisees/Sketch 4.3.pdf

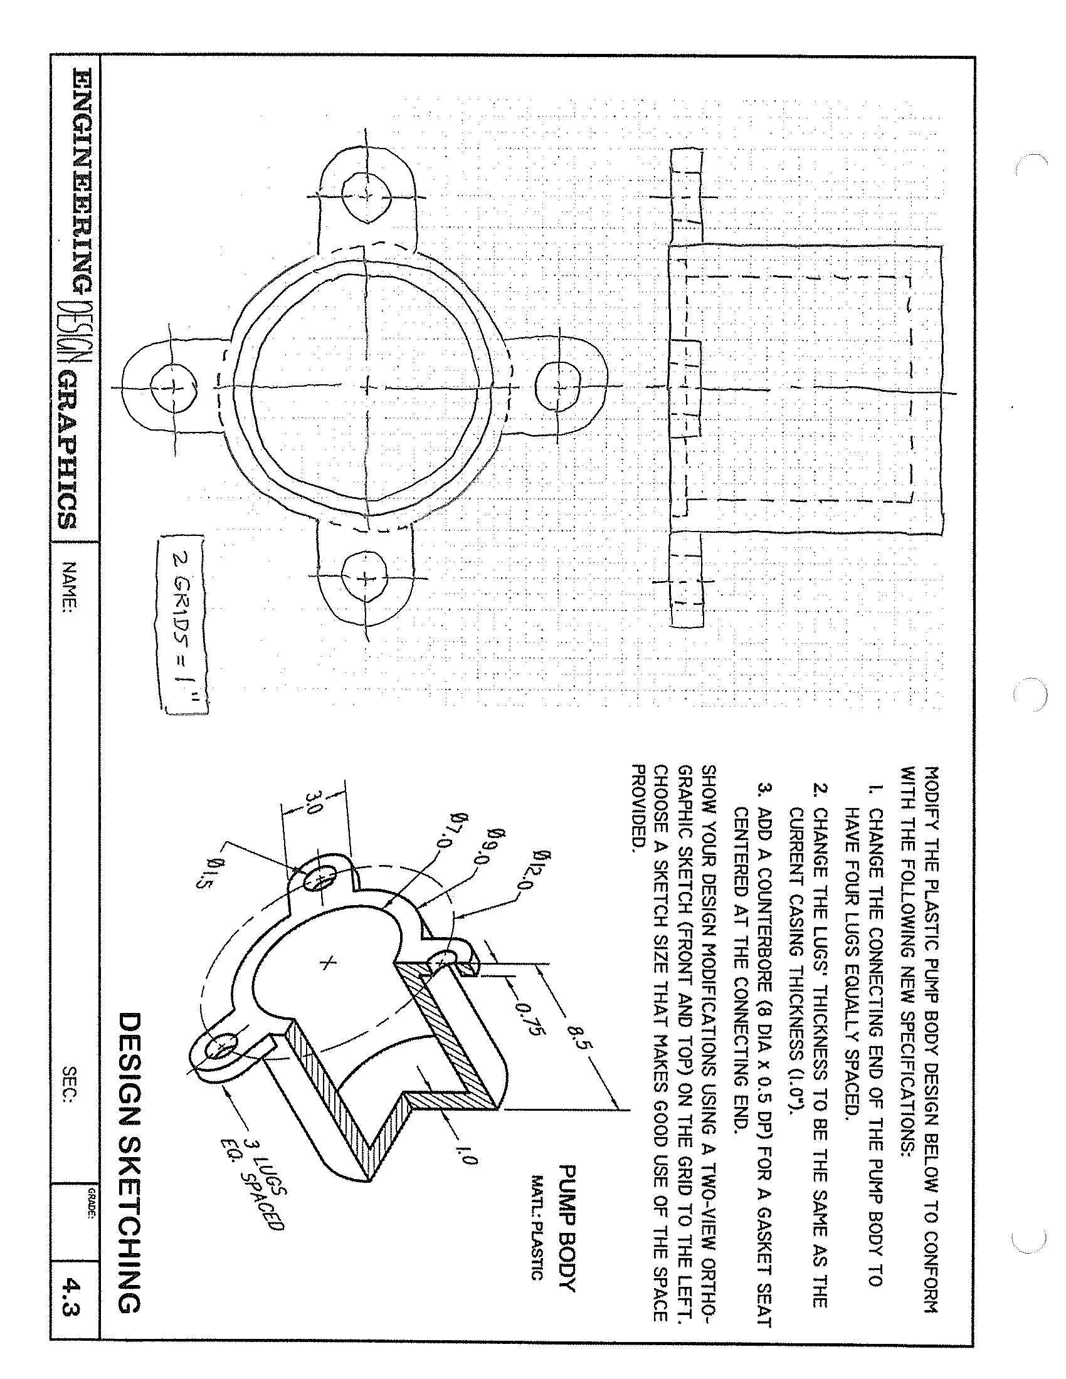
[picture p157: page 1]
