JCam98/me210-engineering-design-graphics/Assignments/Sketches - Exercisees/Sketch 4.4.pdf

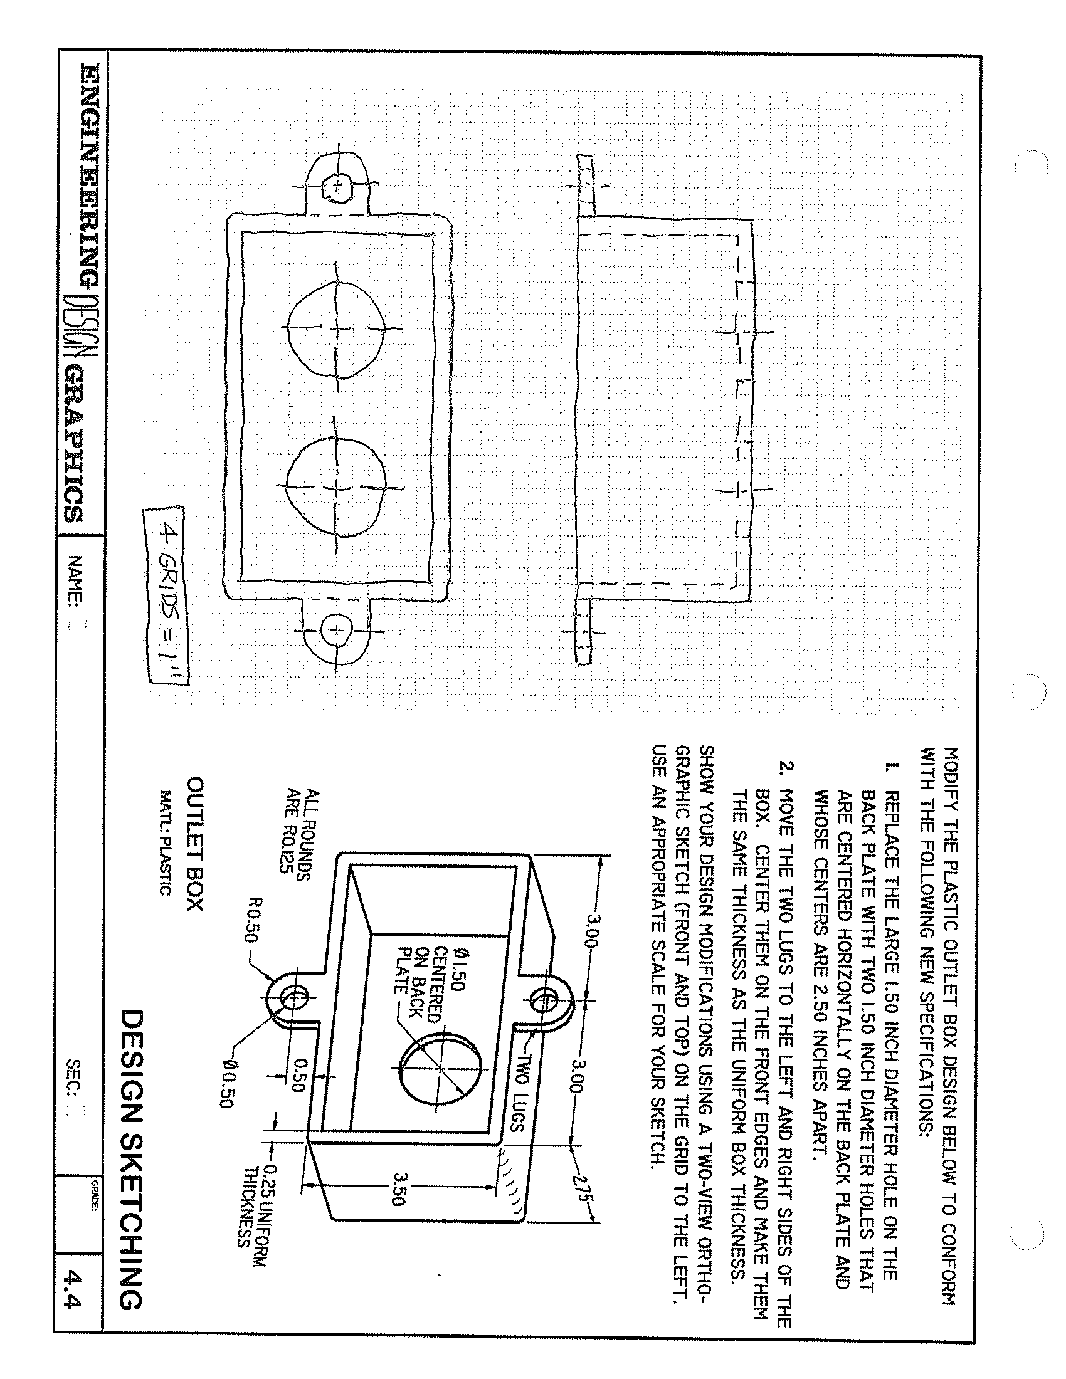
[picture p158: page 1]
