JCam98/me210-engineering-design-graphics/Assignments/Sketches - Exercisees/Sketch 4.5.pdf

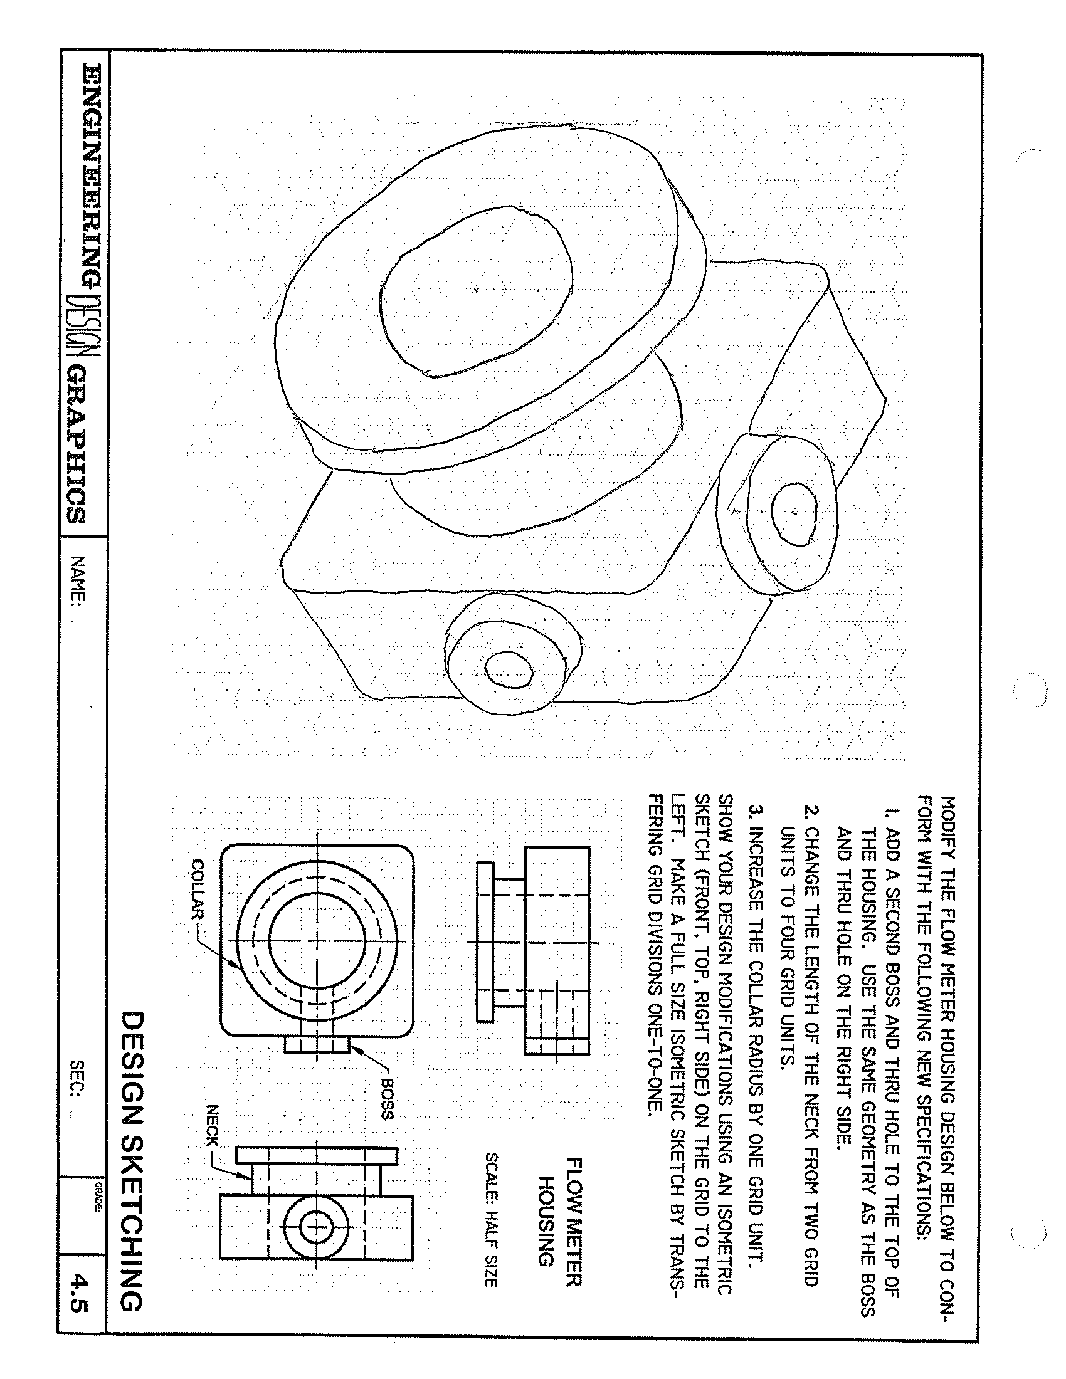
[picture p159: page 1]
