JCam98/me210-engineering-design-graphics/Assignments/Reverse Engineering Project/Design Checks/Design_Check_2/Dissection_Notes/Full_Dissection/IMG-2682.JPG

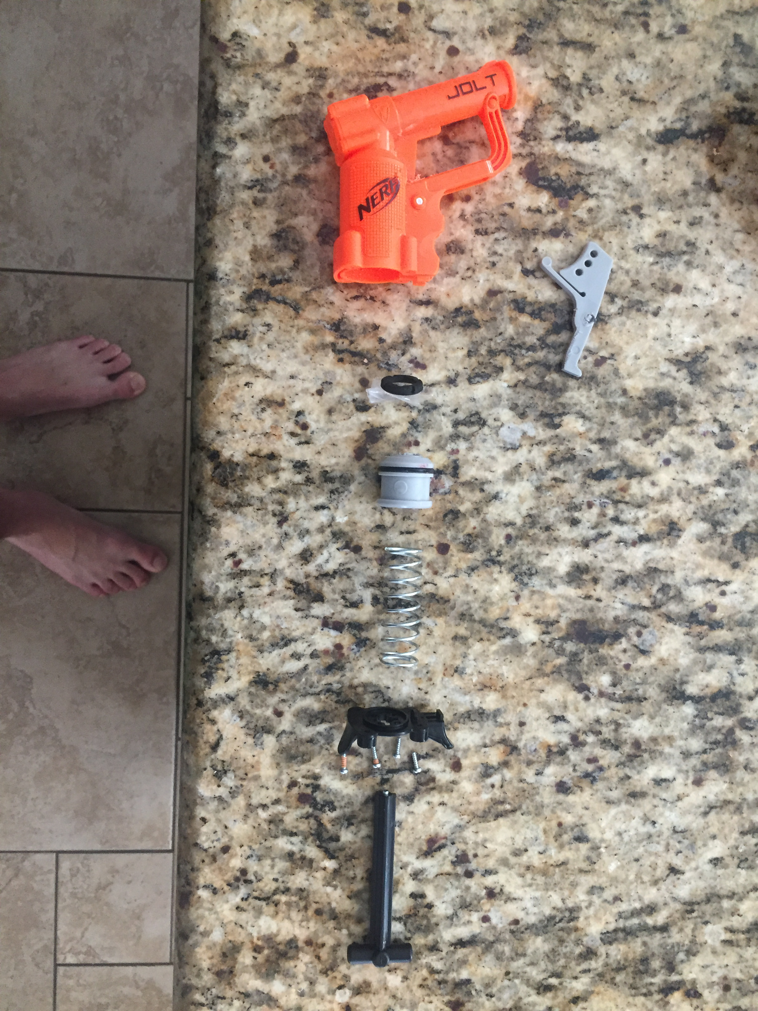
Assignments/Reverse Engineering Project/Design Checks/Design_Check_2/Dissection_Notes/Full_Dissection/IMG-2682.JPG
