JCam98/me210-engineering-design-graphics/Assignments/Reverse Engineering Project/Design Checks/Design_Check_6/Screen Shot 2020-11-17 at 2.04.14 PM.png

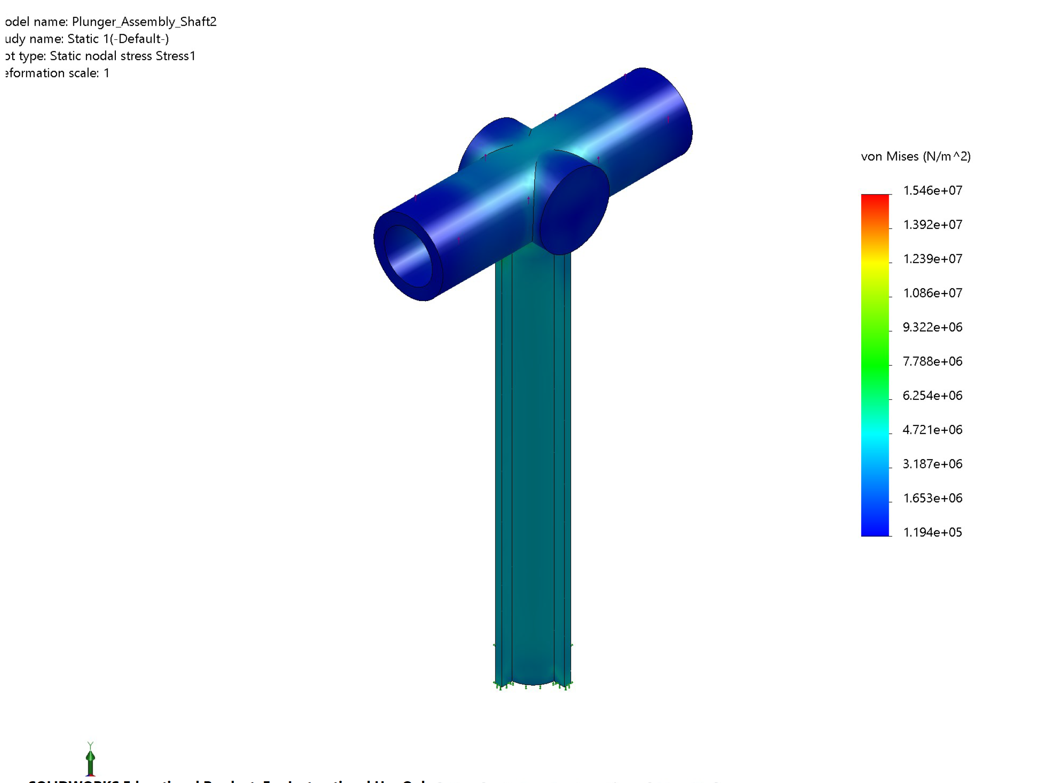
Assignments/Reverse Engineering Project/Design Checks/Design_Check_6/Screen Shot 2020-11-17 at 2.04.14 PM.png
