JCam98/me210-engineering-design-graphics/Assignments/Reverse Engineering Project/Design Checks/Design_Check_6/Screenshot_of_Child_Strength_Values.png

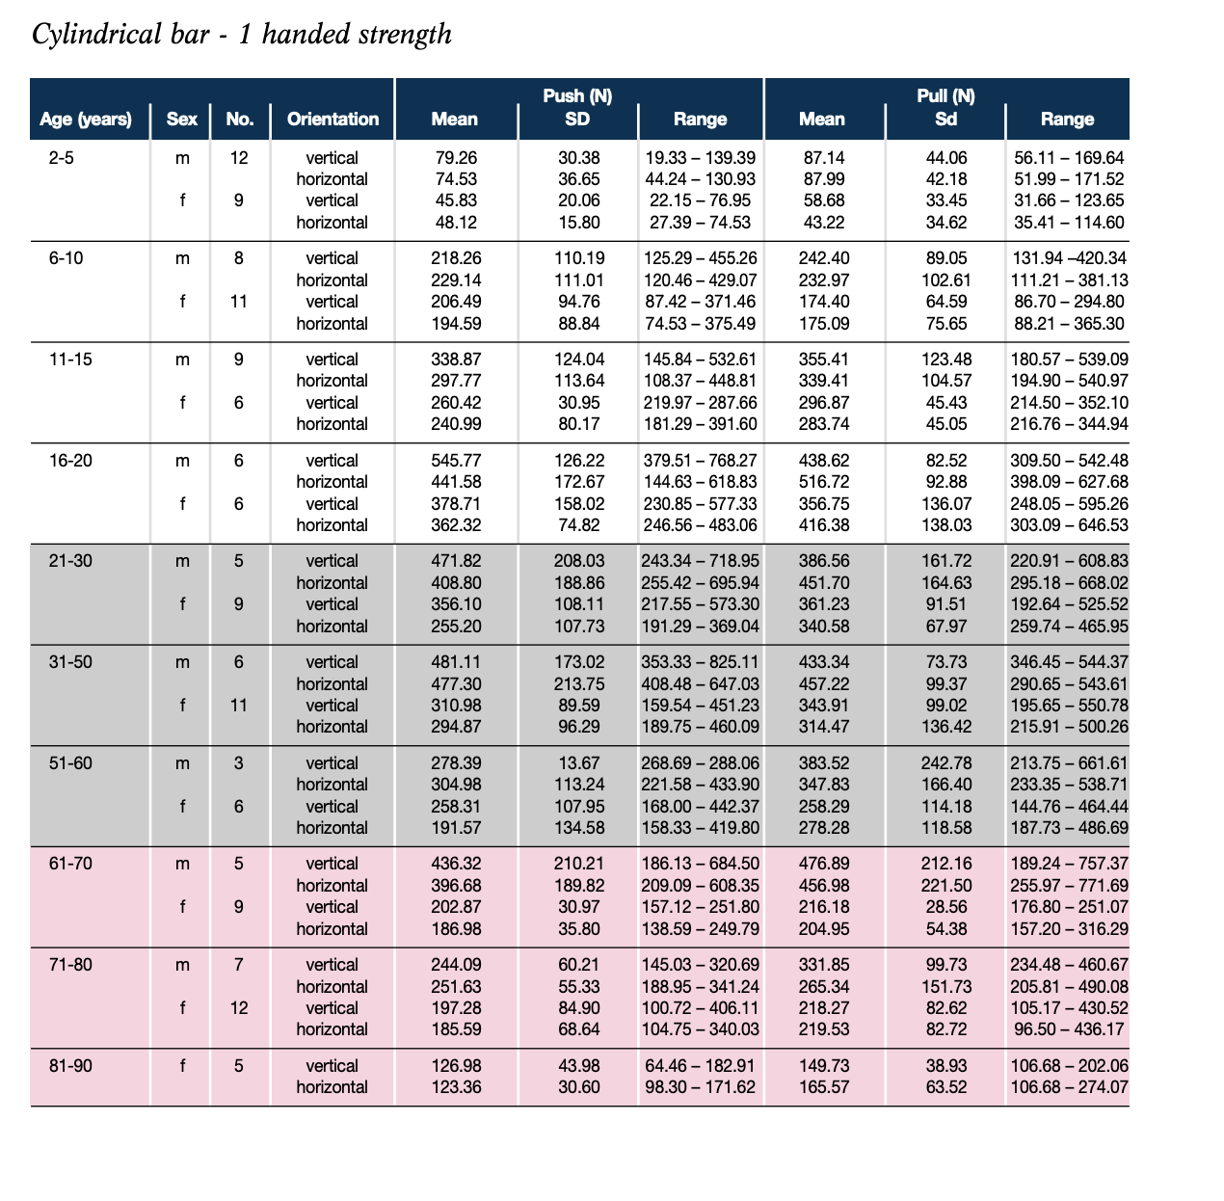
Assignments/Reverse Engineering Project/Design Checks/Design_Check_6/Screenshot_of_Child_Strength_Values.png
