JCam98/me210-engineering-design-graphics/Assignments/Sketches - Exercisees/keyway.jpg

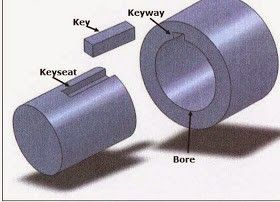
Assignments/Sketches - Exercisees/keyway.jpg
