JCam98/me210-engineering-design-graphics/Assignments/Reverse Engineering Project/Design Checks/Design_Check_4/Part_Files /PLASTIC_CASE_fixed_barrel.SLDPRT

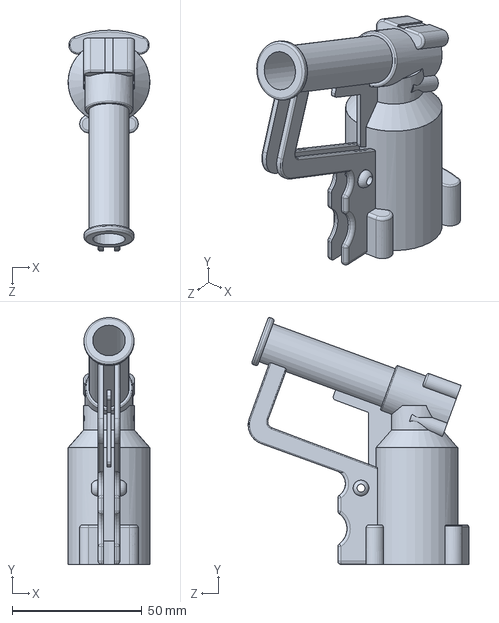
[picture p192: CAD file, 2026-01-26]
Assignments/Reverse Engineering Project/Design Checks/Design_Check_4/Part_Files /PLASTIC_CASE_fixed_barrel.SLDPRT
31.5 x 95.1 x 85.0 mm
