JCam98/me210-engineering-design-graphics/Assignments/Reverse Engineering Project/Design Checks/Design_Check_4/Part_Files /BASE_PLATE.SLDPRT

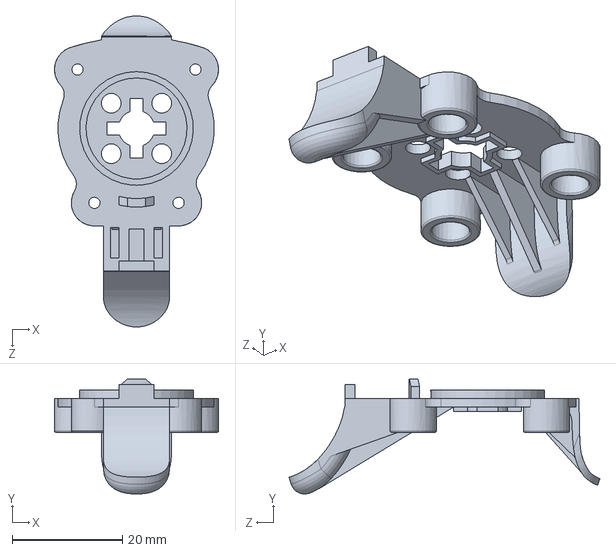
[picture p193: CAD file, 2026-01-26]
Assignments/Reverse Engineering Project/Design Checks/Design_Check_4/Part_Files /BASE_PLATE.SLDPRT
29.7 x 20.8 x 56.3 mm
