JCam98/me210-engineering-design-graphics/Assignments/Reverse Engineering Project/Design Checks/Design_Check_4/Part_Files /7_rubber_o-ring.SLDPRT

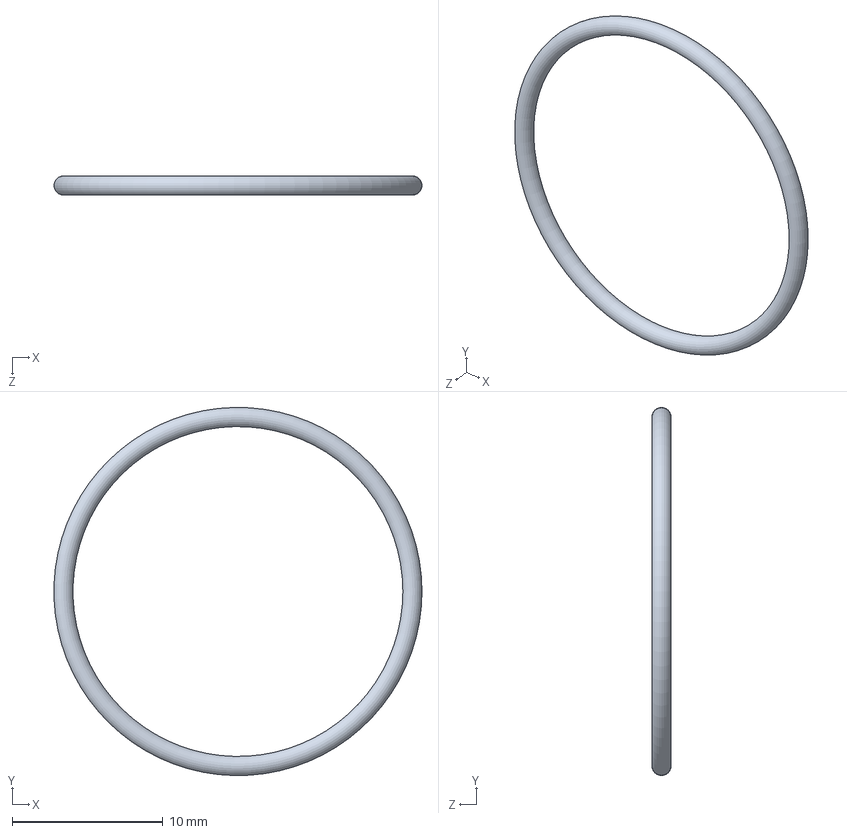
[picture p194: CAD file, 2026-01-26]
Assignments/Reverse Engineering Project/Design Checks/Design_Check_4/Part_Files /7_rubber_o-ring.SLDPRT
24.4 x 24.4 x 1.27 mm
