JCam98/me210-engineering-design-graphics/Assignments/Reverse Engineering Project/Design Checks/Design_Check_4/Part_Files /5_vacuum_spring.SLDPRT

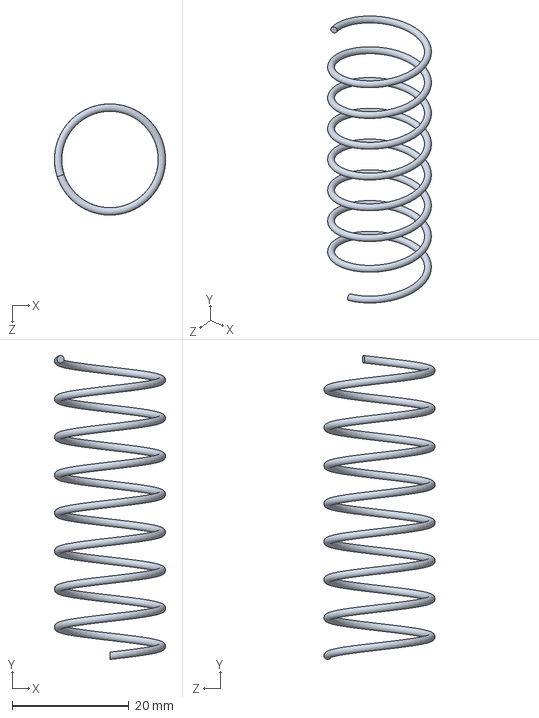
[picture p195: CAD file, 2026-01-26]
Assignments/Reverse Engineering Project/Design Checks/Design_Check_4/Part_Files /5_vacuum_spring.SLDPRT
19.0 x 52.1 x 19.0 mm
