JCam98/me210-engineering-design-graphics/Assignments/Reverse Engineering Project/Design Checks/Design_Check_4/PDFS/HOUSINGASSEMBLY.pdf

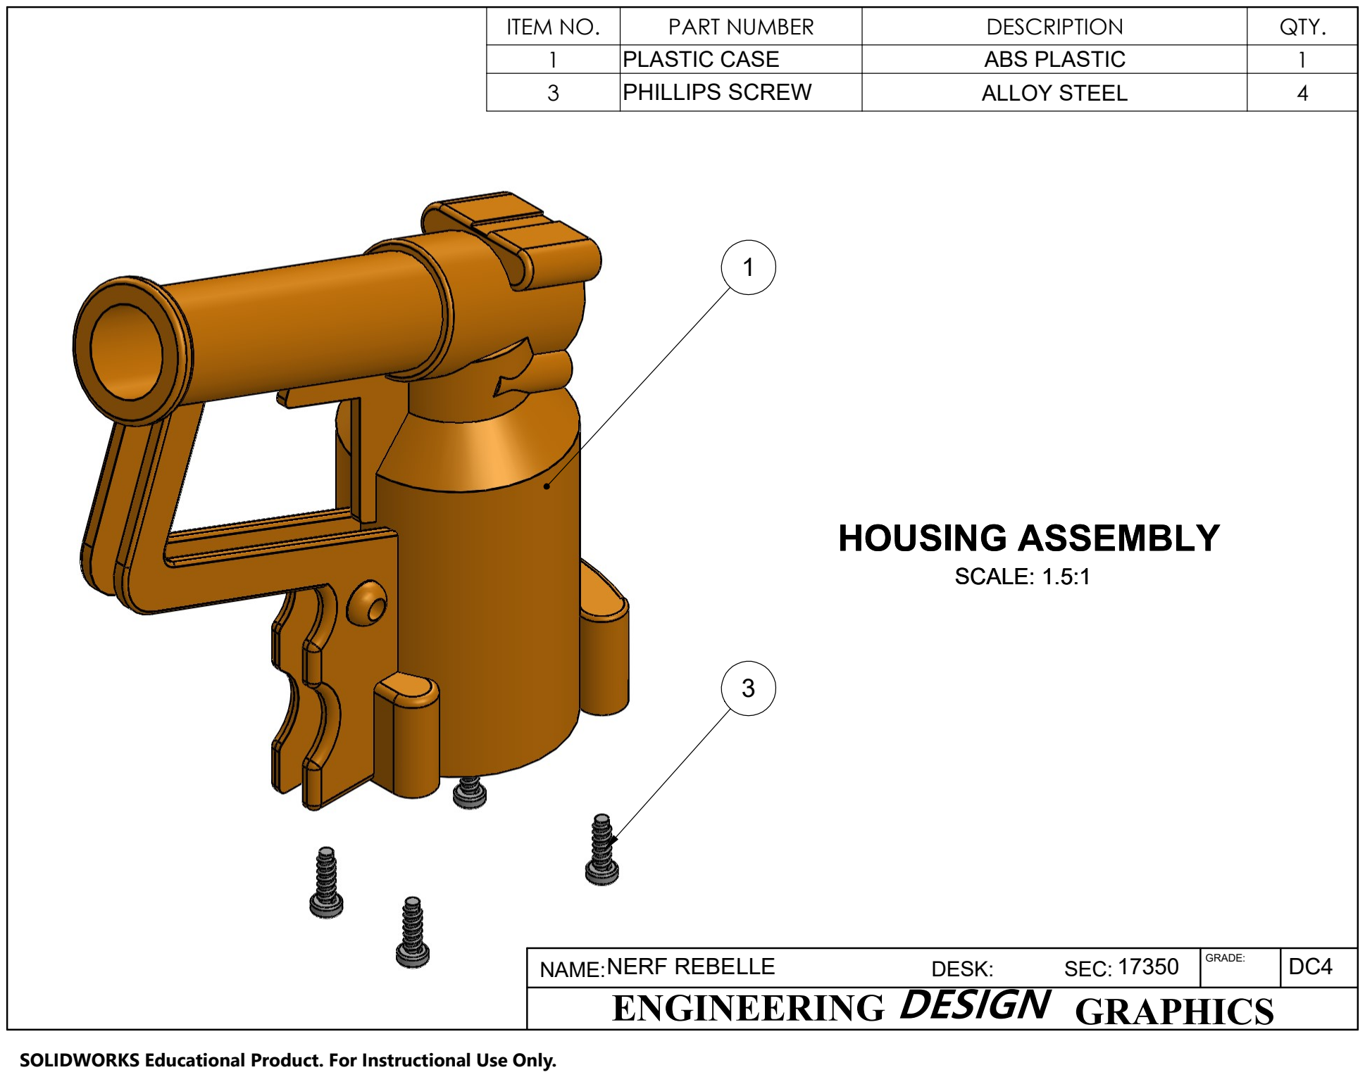
[picture p196: page 1]

# GRAPHICS

NAME: | DESK: | GRADE:

# ENGINEERING DESIGN

SEC:

1

3

NERF REBELLE

ITEM NO. | PART NUMBER | DESCRIPTION | QTY.
1 | PLASTIC CASE | ABS PLASTIC | 1
3 | PHILLIPS SCREW | ALLOY STEEL | 4

17350 DC4

## HOUSING ASSEMBLY

SCALE: 1.5:1

SOLIDWORKS Educational Product. For Instructional Use Only.
