JCam98/me210-engineering-design-graphics/Assignments/Reverse Engineering Project/Design Checks/Design_Check_4/PDFS/Plunger_Assembly_Shaft.pdf

# SHAFT

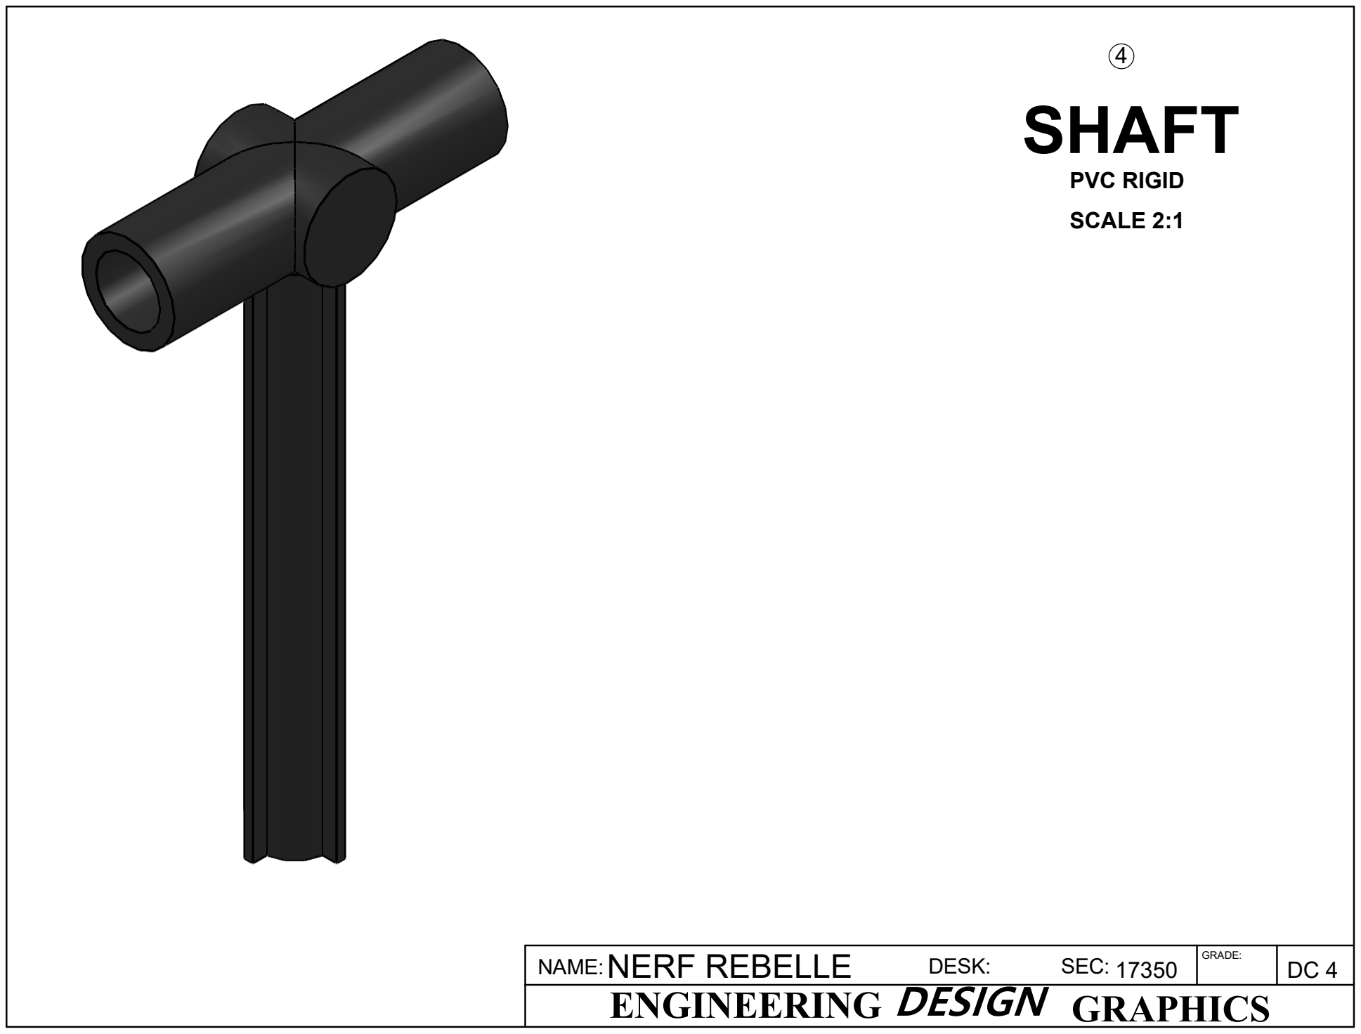
[picture p197: page 1]

NAME: | DESK: | GRADE:
D E S I G N ENGINEERING | GRAPHICS
NERF REBELLE | SEC: 17350 | DC 4

4

SCALE 2:1

PVC RIGID
