JCam98/me210-engineering-design-graphics/Assignments/Reverse Engineering Project/Design Checks/Design_Check_4/PDFS/Plunger_Assembly_Shaft_Head.pdf

# Shaft Head

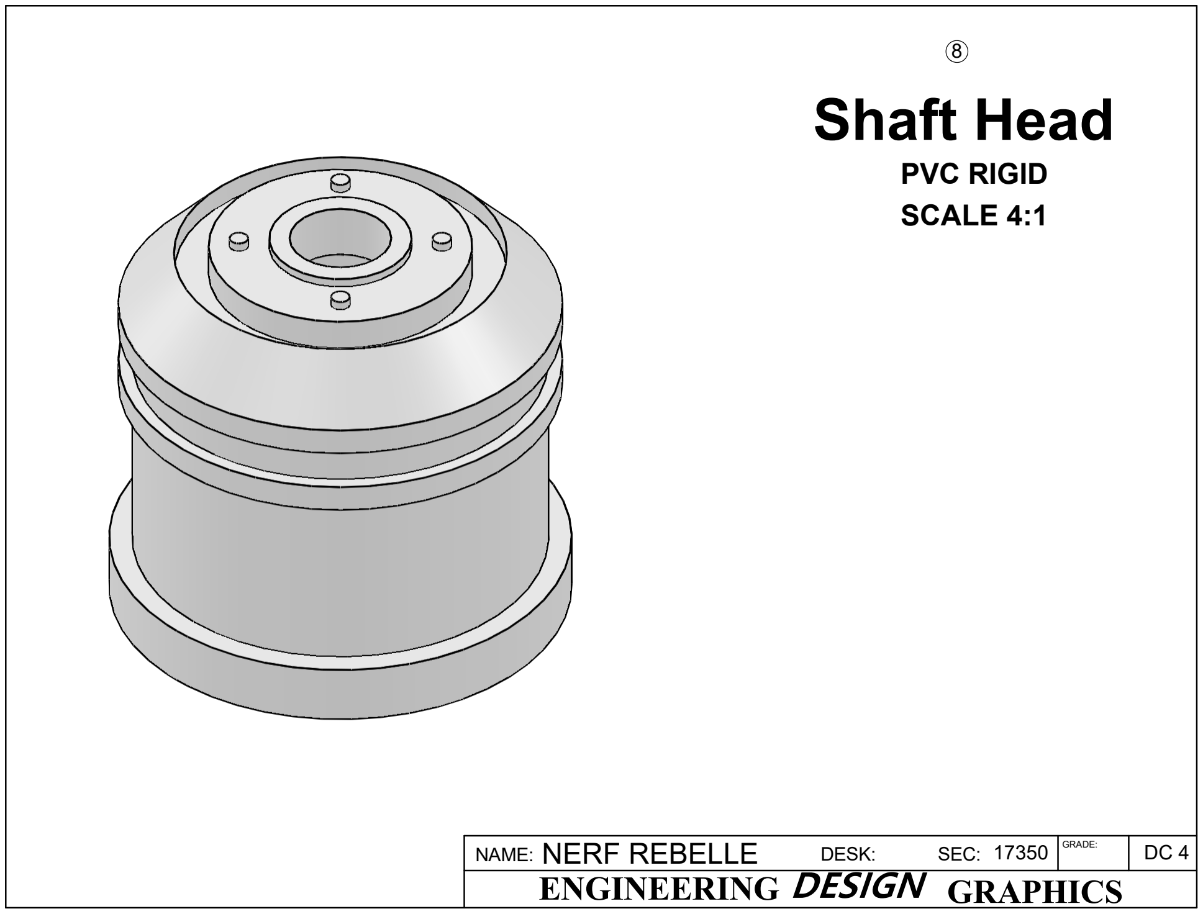
[picture p198: page 1]

ENGINEERING | GRAPHICS
NAME: | DESK: | GRADE:
D E S I G N

SEC:

8

17350 | DC 4

SCALE 4:1

PVC RIGID

NERF REBELLE
