JCam98/me210-engineering-design-graphics/Assignments/Reverse Engineering Project/Design Checks/Design_Check_4/PDFS/10_TRIGGER_RIVET_.pdf

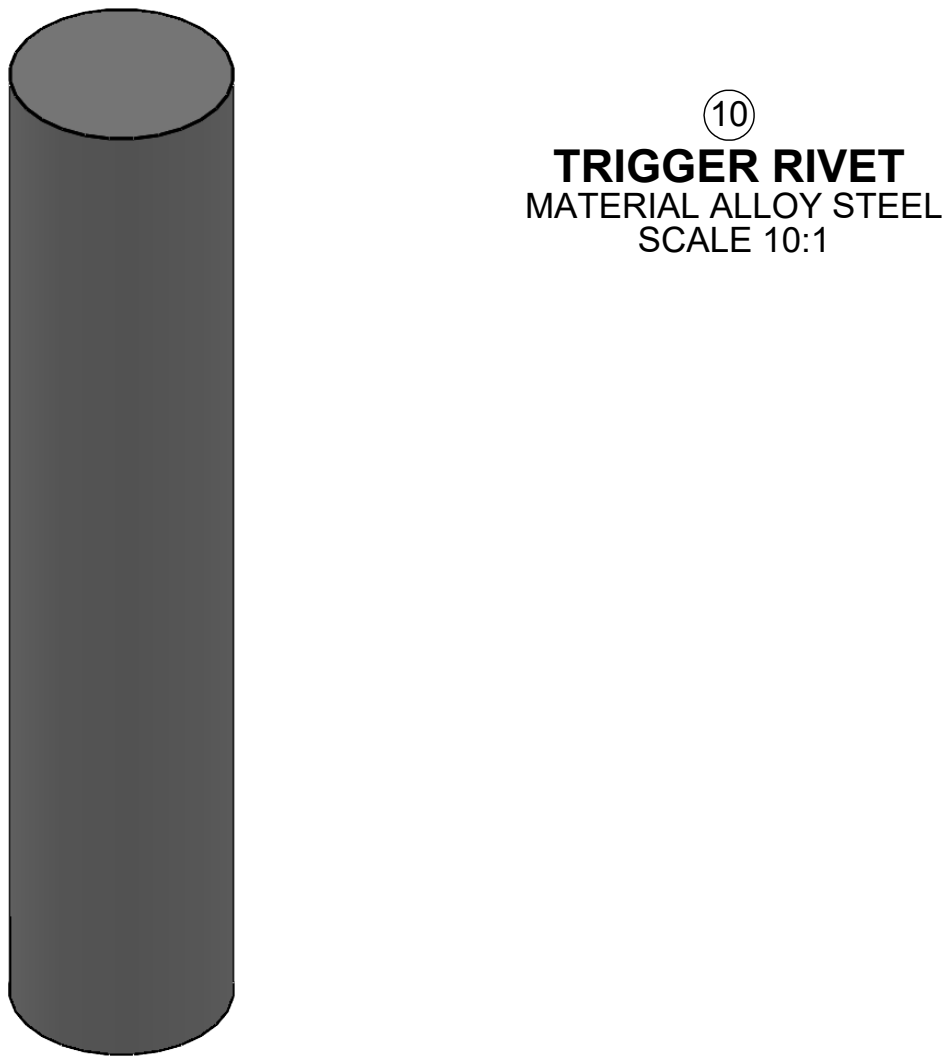
[picture p267: page 1]
NERF REBELLE; NAME:; DESK:; GRADE: SEC:

TRIGGER RIVET
MATERIAL ALLOY STEEL
SCALE 10:1

ENGINEERING DESIGN GRAPHICS

SOLIDWORKS Educational Product. For Instructional Use Only.
