JCam98/me210-engineering-design-graphics/Assignments/Reverse Engineering Project/Design Checks/Design_Check_4/PDFS/11_TRIGGER.pdf

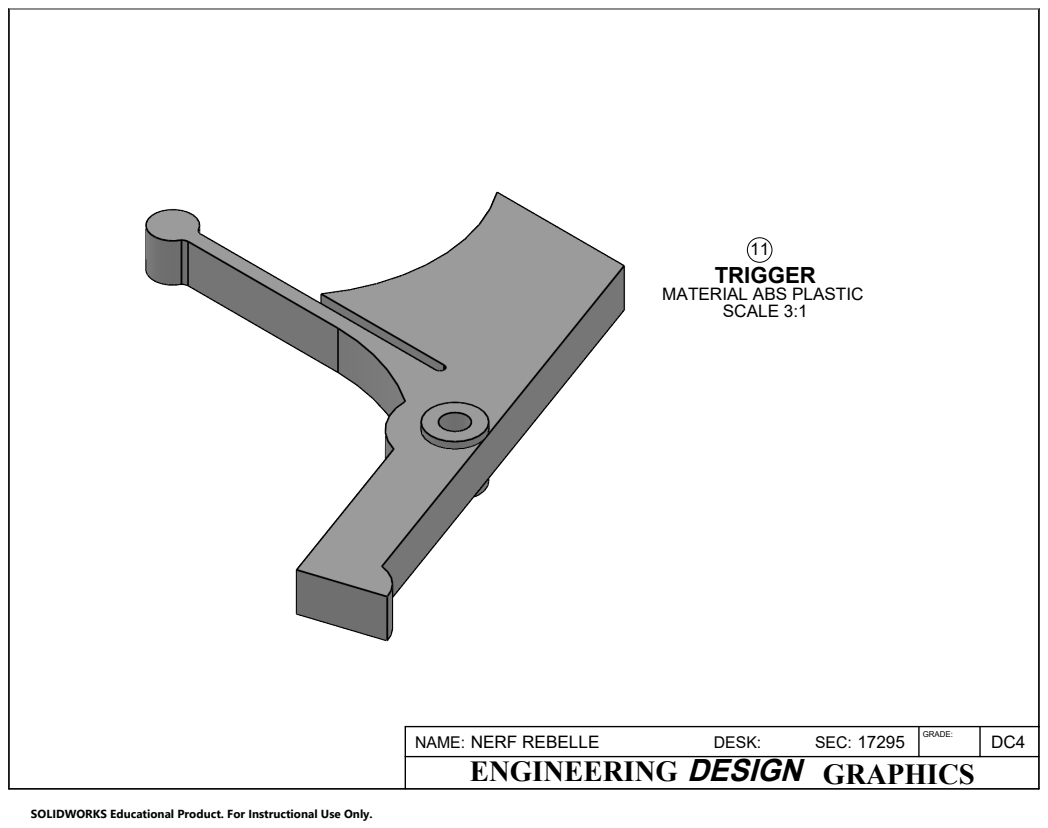
[picture p268: page 1]
MATERIAL ABS PLASTIC SCALE 3:1; NERF REBELLE; NAME:; DESK:; GRADE: SEC:

ENGINEERING DESIGN GRAPHICS

SOLIDWORKS Educational Product. For Instructional Use Only.
