JCam98/me210-engineering-design-graphics/Assignments/Reverse Engineering Project/Design Checks/Design_Check_4/PDFS/7_RUBBER_O_RING.pdf

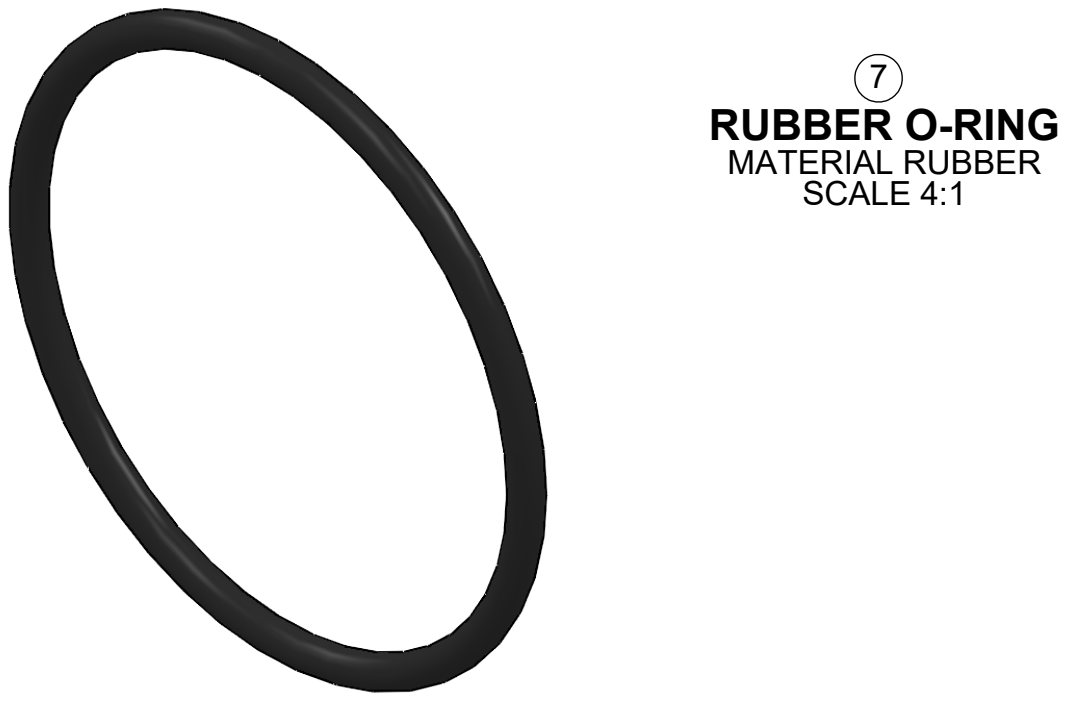
[picture p269: page 1]
NERF REBELLE; RUBBER O-RING MATERIAL RUBBER SCALE 4:1; NAME:; DESK:; GRADE: SEC:

ENGINEERING DESIGN GRAPHICS

SOLIDWORKS Educational Product. For Instructional Use Only.
