JCam98/me210-engineering-design-graphics/Assignments/Reverse Engineering Project/Design Checks/Design_Check_4/PDFS/Firing_Barrel_Assembly.pdf

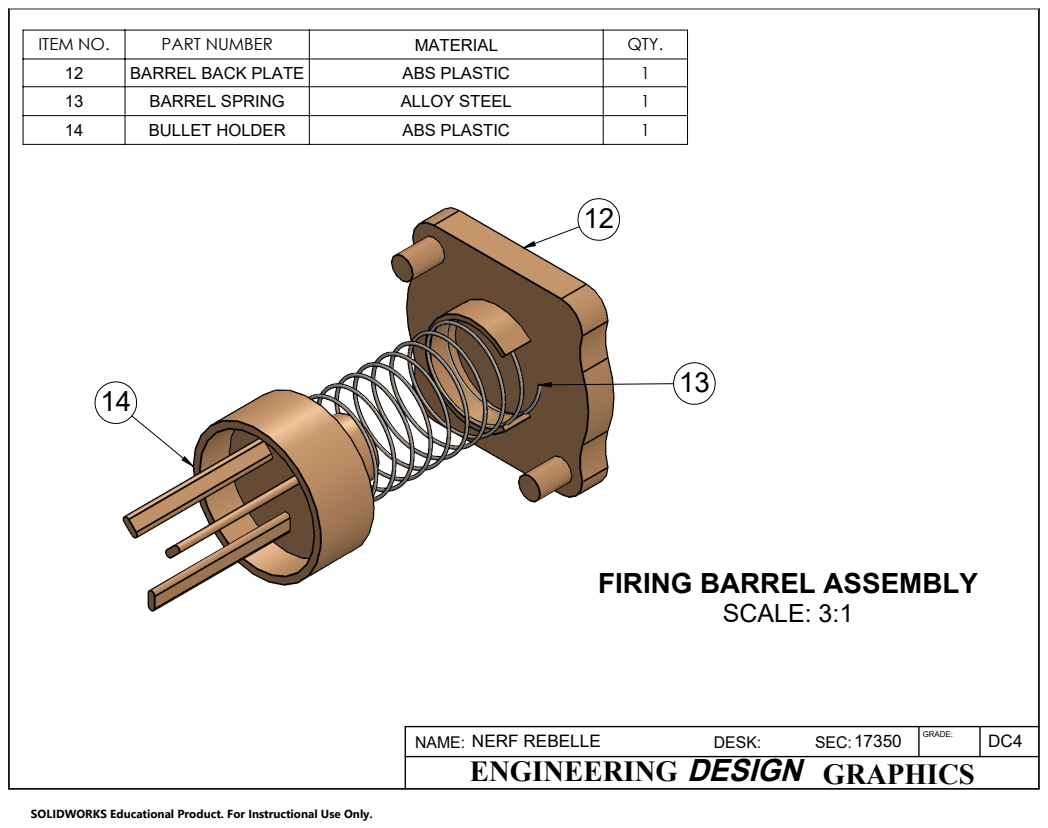
[picture p270: page 1]
NERF REBELLE; SCALE: 3:1; NAME:; DESK:; GRADE: SEC:

ITEM NO. | PART NUMBER | MATERIAL | QTY.
12 | BARREL BACK PLATE | ABS PLASTIC | 1
13 | BARREL SPRING | ALLOY STEEL | 1
14 | BULLET HOLDER | ABS PLASTIC | 1

FIRING BARREL ASSEMBLY

ENGINEERING DESIGN GRAPHICS

SOLIDWORKS Educational Product. For Instructional Use Only.
