JCam98/me210-engineering-design-graphics/Assignments/Reverse Engineering Project/Design Checks/Design_Check_4/PDFS/Part_12_-_Barrel_Back_Plate.pdf

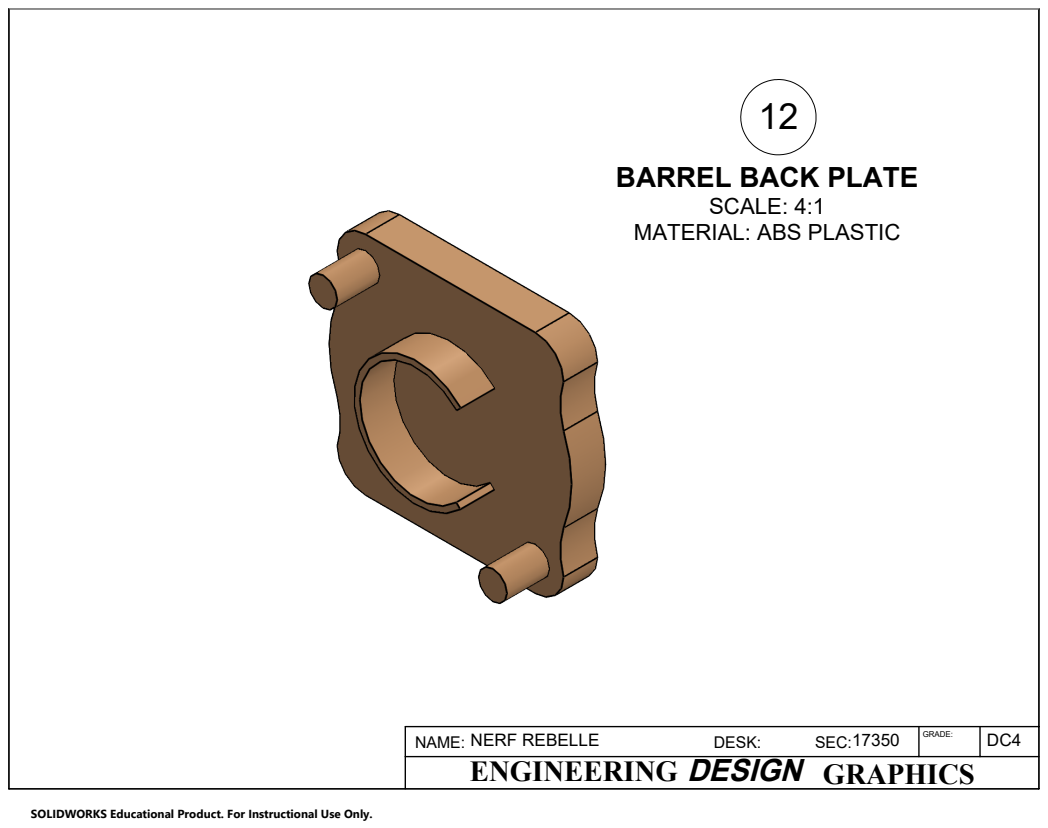
[picture p271: page 1]
NERF REBELLE; NAME:; DESK:; GRADE: SEC:

BARREL BACK PLATE

SCALE: 4:1
MATERIAL: ABS PLASTIC

ENGINEERING DESIGN GRAPHICS

SOLIDWORKS Educational Product. For Instructional Use Only.
