JCam98/me210-engineering-design-graphics/Assignments/Reverse Engineering Project/Design Checks/Design_Check_4/PDFS/Part_13_-_Barrel_Spring.pdf

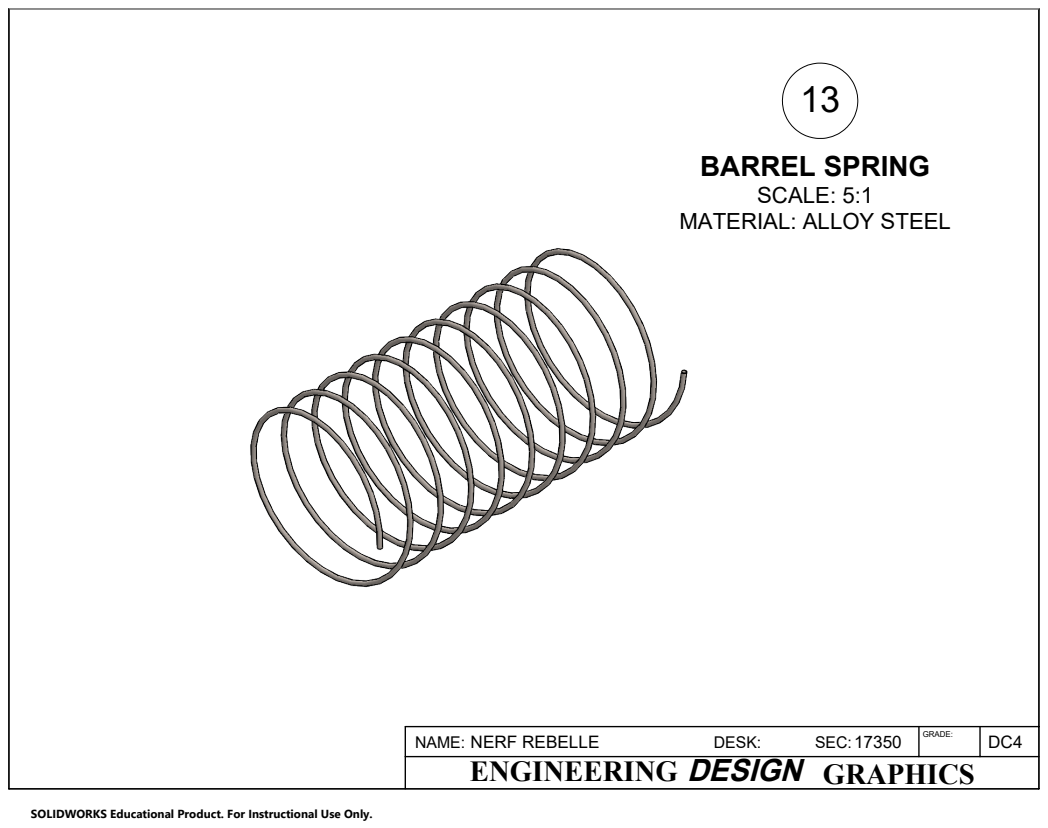
[picture p272: page 1]
NERF REBELLE; NAME:; DESK:; GRADE: SEC:

BARREL SPRING
SCALE: 5:1
MATERIAL: ALLOY STEEL

ENGINEERING DESIGN GRAPHICS

SOLIDWORKS Educational Product. For Instructional Use Only.
