JCam98/me210-engineering-design-graphics/Assignments/Reverse Engineering Project/Design Checks/Design_Check_4/PDFS/Part_14_-_Bullet_Holder.pdf

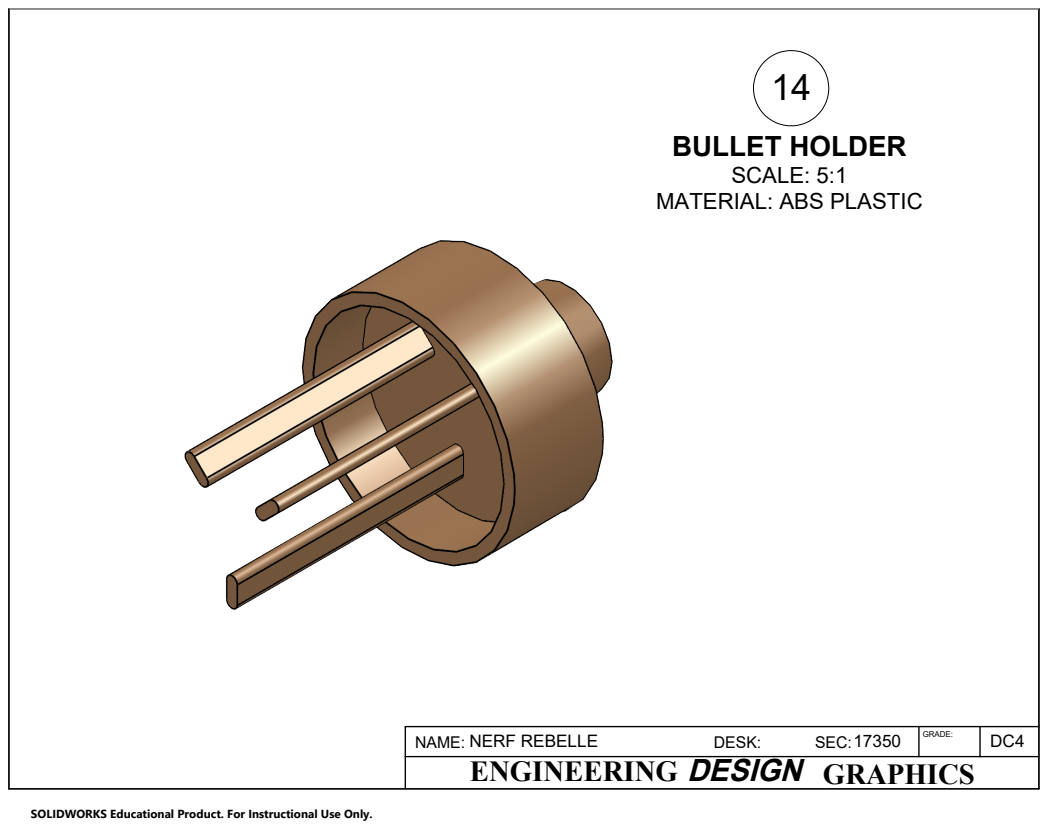
[picture p273: page 1]
NERF REBELLE; NAME:; DESK:; GRADE: SEC:

BULLET HOLDER
SCALE: 5:1
MATERIAL: ABS PLASTIC

ENGINEERING DESIGN GRAPHICS

SOLIDWORKS Educational Product. For Instructional Use Only.
