JCam98/me210-engineering-design-graphics/Assignments/Reverse Engineering Project/Design Checks/Design_Check_4/PDFS/RUBBER_SEAL.PDF

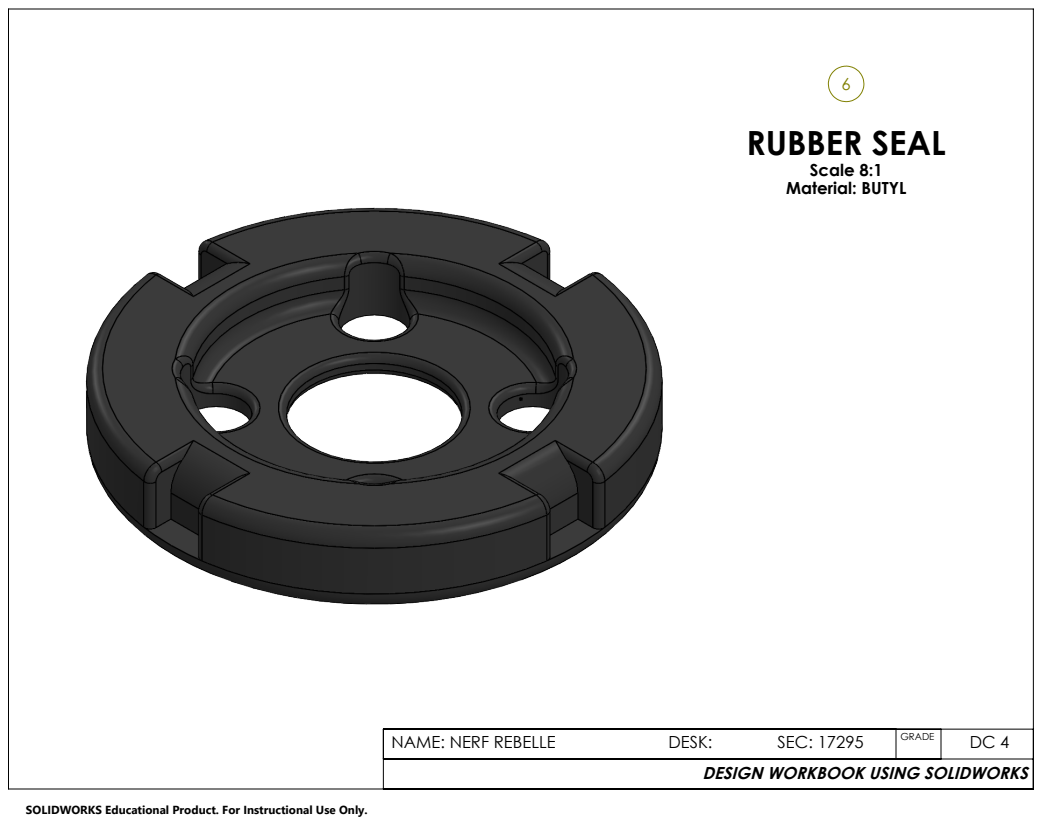
[picture p274: page 1]
RUBBER SEAL; Scale 8:1 Material: BUTYL; NAME: NERF REBELLE; DESK:; SEC: 17295; GRADE

DESIGN WORKBOOK USING SOLIDWORKS

SOLIDWORKS Educational Product. For Instructional Use Only.
