JCam98/me210-engineering-design-graphics/Assignments/Reverse Engineering Project/Design Checks/Design_Check_4/PDFS/TOTAL_ASSEMBLY.pdf

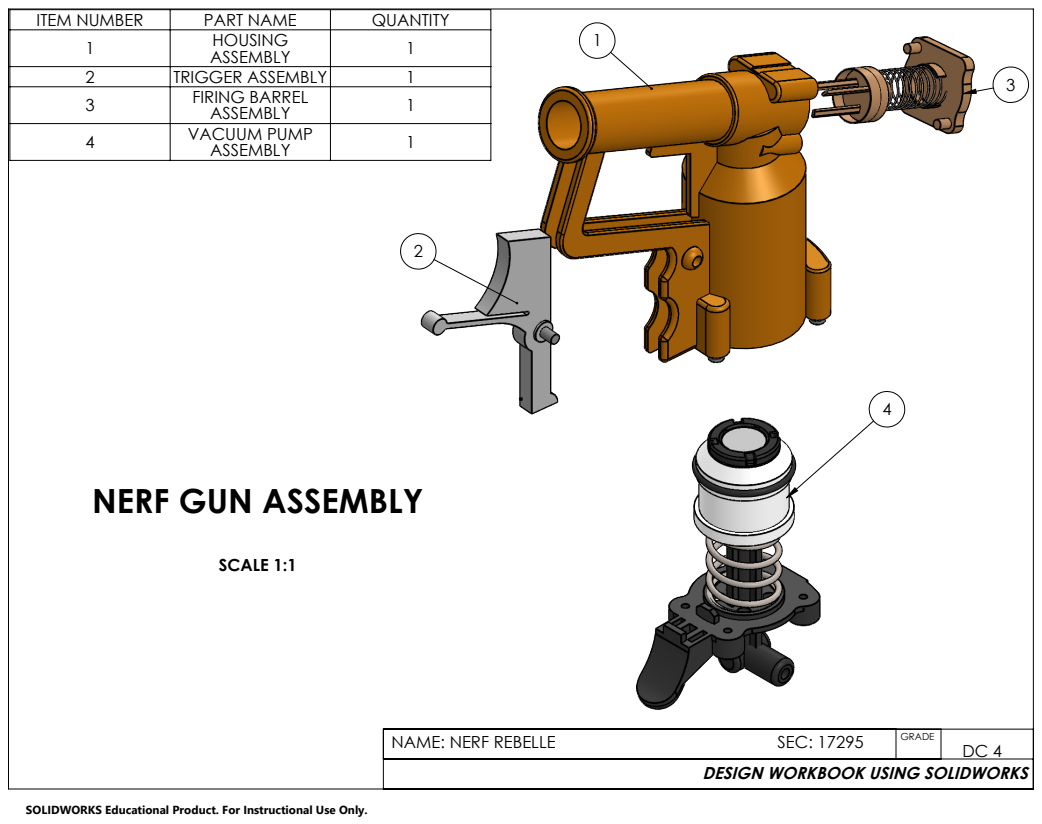
[picture p275: page 1]
SCALE 1:1; NAME: NERF REBELLE; SEC: 17295; GRADE

ITEM NUMBER | PART NAME | QUANTITY
1 | HOUSING ASSEMBLY | 1
2 | TRIGGER ASSEMBLY | 1
3 | FIRING BARREL ASSEMBLY | 1
4 | VACUUM PUMP ASSEMBLY | 1

NERF GUN ASSEMBLY

DESIGN WORKBOOK USING SOLIDWORKS

SOLIDWORKS Educational Product. For Instructional Use Only.
