JCam98/me210-engineering-design-graphics/Assignments/Reverse Engineering Project/Design Checks/Design_Check_4/PDFS/TRIGGER_ASSEMBLY.pdf

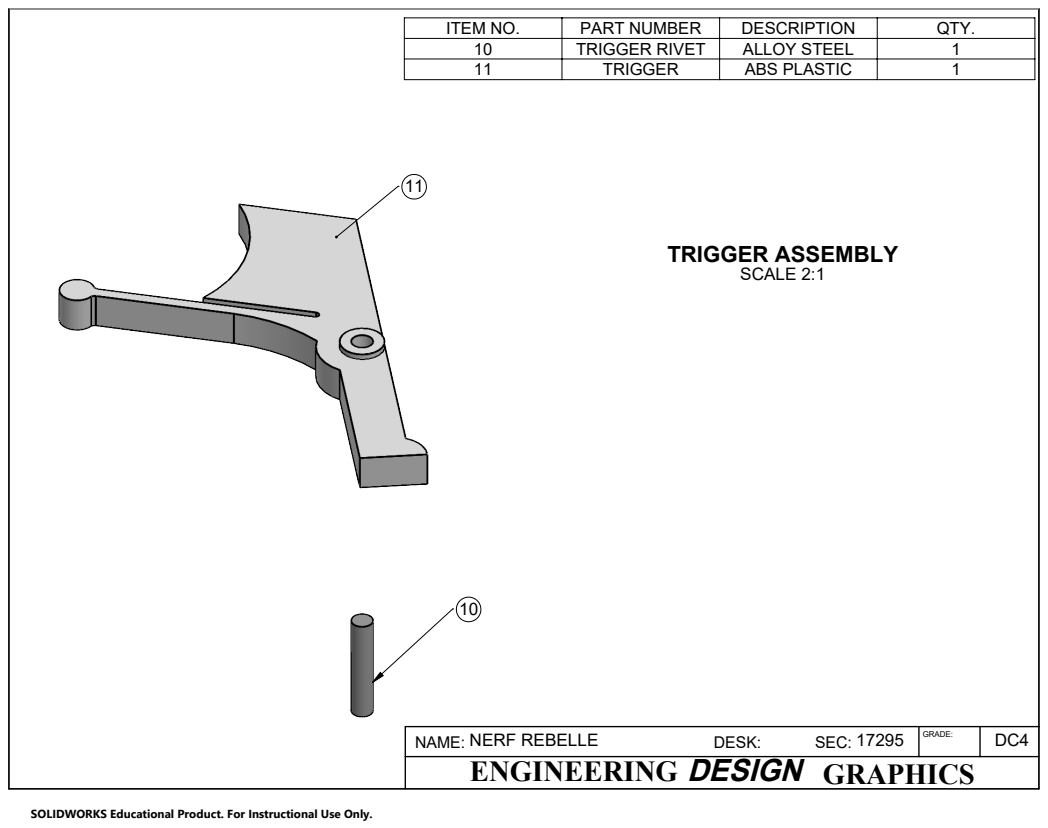
[picture p276: page 1]
NERF REBELLE; TRIGGER ASSEMBLY SCALE 2:1; NAME:; DESK:; GRADE: SEC:

ITEM NO. | PART NUMBER | DESCRIPTION | QTY.
10 | TRIGGER RIVET | ALLOY STEEL | 1
11 | TRIGGER | ABS PLASTIC | 1

ENGINEERING DESIGN GRAPHICS

SOLIDWORKS Educational Product. For Instructional Use Only.
