JCam98/me210-engineering-design-graphics/Assignments/Reverse Engineering Project/Design Checks/Design_Check_4/PDFS/VACUUM_PUMP_Assembly.pdf

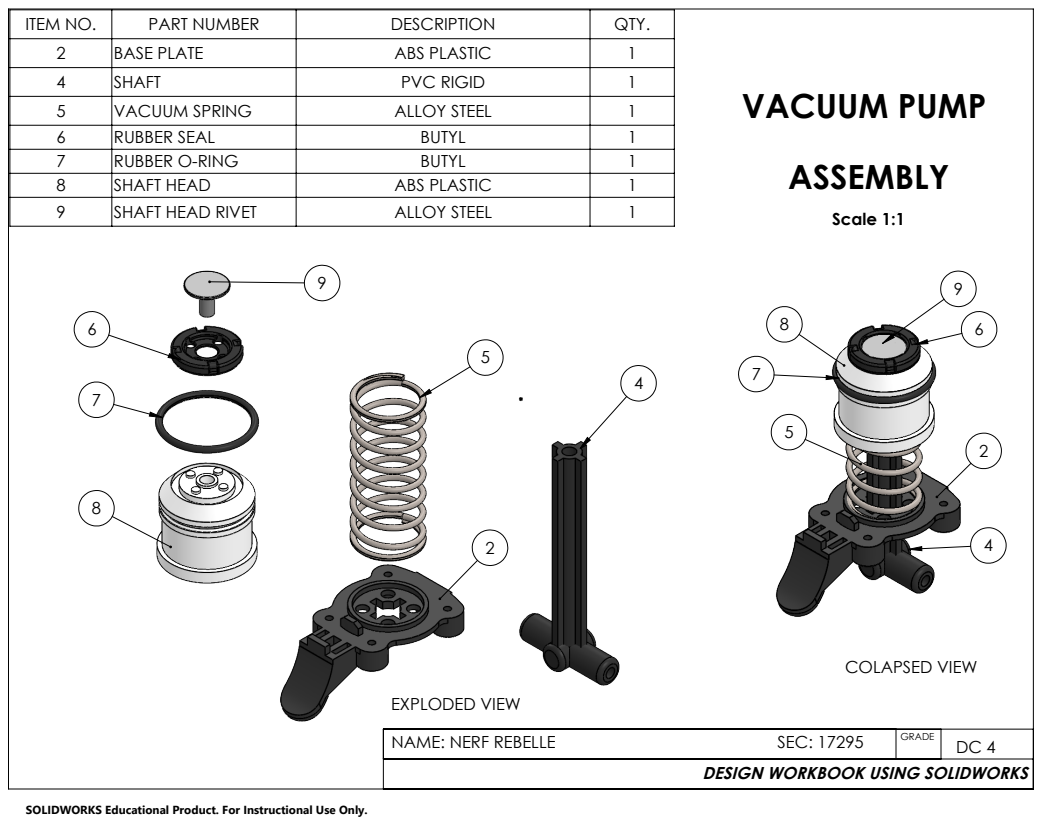
[picture p277: page 1]
EXPLODED VIEW; COLAPSED VIEW; VACUUM PUMP; Scale 1:1; NAME: NERF REBELLE; SEC: 17295; GRADE

ITEM NO. | PART NUMBER | DESCRIPTION | QTY.
2 | BASE PLATE | ABS PLASTIC | 1
4 | SHAFT | PVC RIGID | 1
5 | VACUUM SPRING | ALLOY STEEL | 1
6 | RUBBER SEAL | BUTYL | 1
7 | RUBBER O-RING | BUTYL | 1
8 | SHAFT HEAD | ABS PLASTIC | 1
9 | SHAFT HEAD RIVET | ALLOY STEEL | 1

DESIGN WORKBOOK USING SOLIDWORKS

SOLIDWORKS Educational Product. For Instructional Use Only.
