JCam98/me210-engineering-design-graphics/Assignments/Reverse Engineering Project/Design Checks/Design_Check_4/PDFS/VACUUM_SPRING.PDF

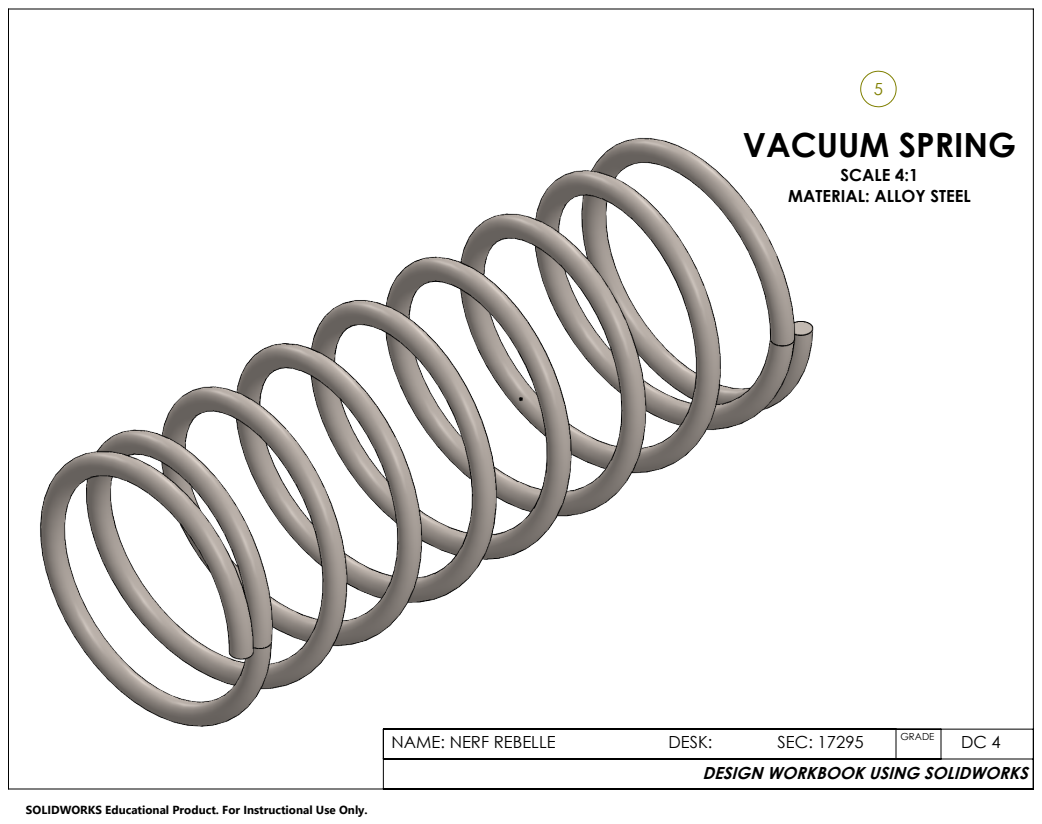
[picture p278: page 1]
VACUUM SPRING; NAME: NERF REBELLE; DESK:; SEC: 17295; GRADE

SCALE 4:1
MATERIAL: ALLOY STEEL

DESIGN WORKBOOK USING SOLIDWORKS

SOLIDWORKS Educational Product. For Instructional Use Only.
