JCam98/me210-engineering-design-graphics/Assignments/Reverse Engineering Project/Drawings/Orthogonal_Drawing_-_Part_14_-_Bullet_Holder.pdf

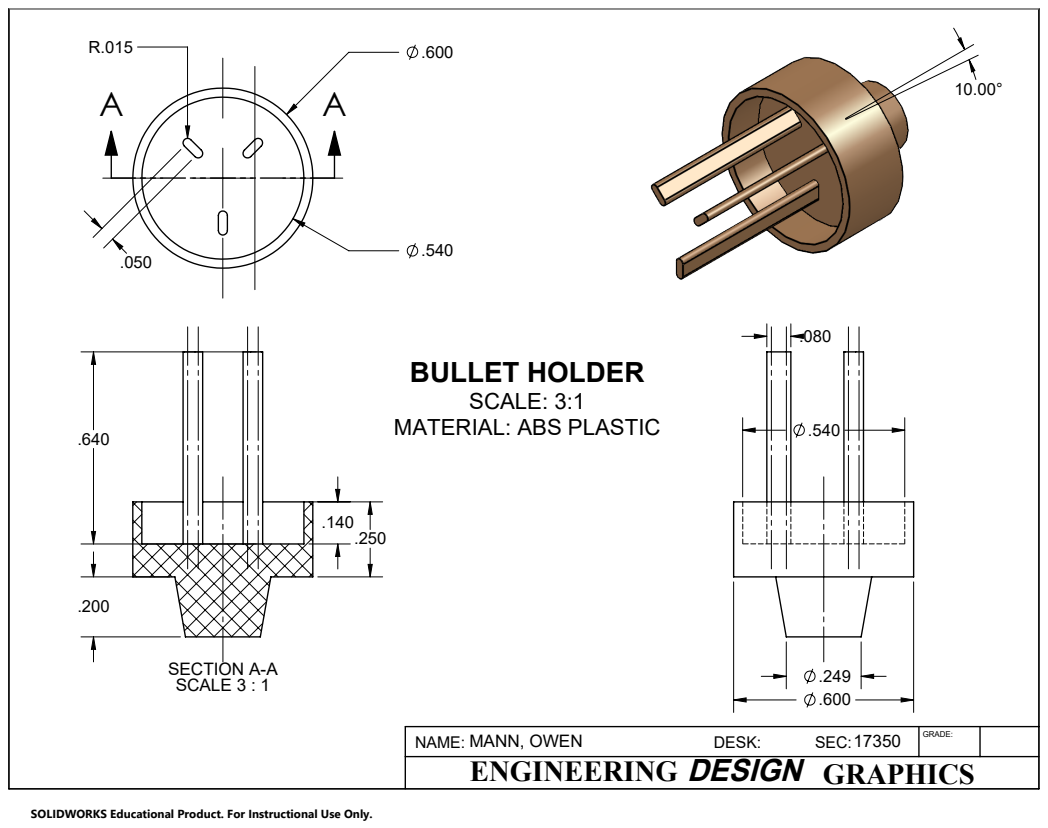
[picture p279: page 1]
SECTION A-A SCALE 3 : 1; MANN, OWEN; NAME:; DESK:; GRADE: SEC:

BULLET HOLDER
SCALE: 3:1
MATERIAL: ABS PLASTIC

ENGINEERING DESIGN GRAPHICS

SOLIDWORKS Educational Product. For Instructional Use Only.
