JCam98/me210-engineering-design-graphics/Assignments/Reverse Engineering Project/Drawings/ORTHOGONAL_PHILLIPS_SCREW.pdf

## PHILLIP'S SCREW

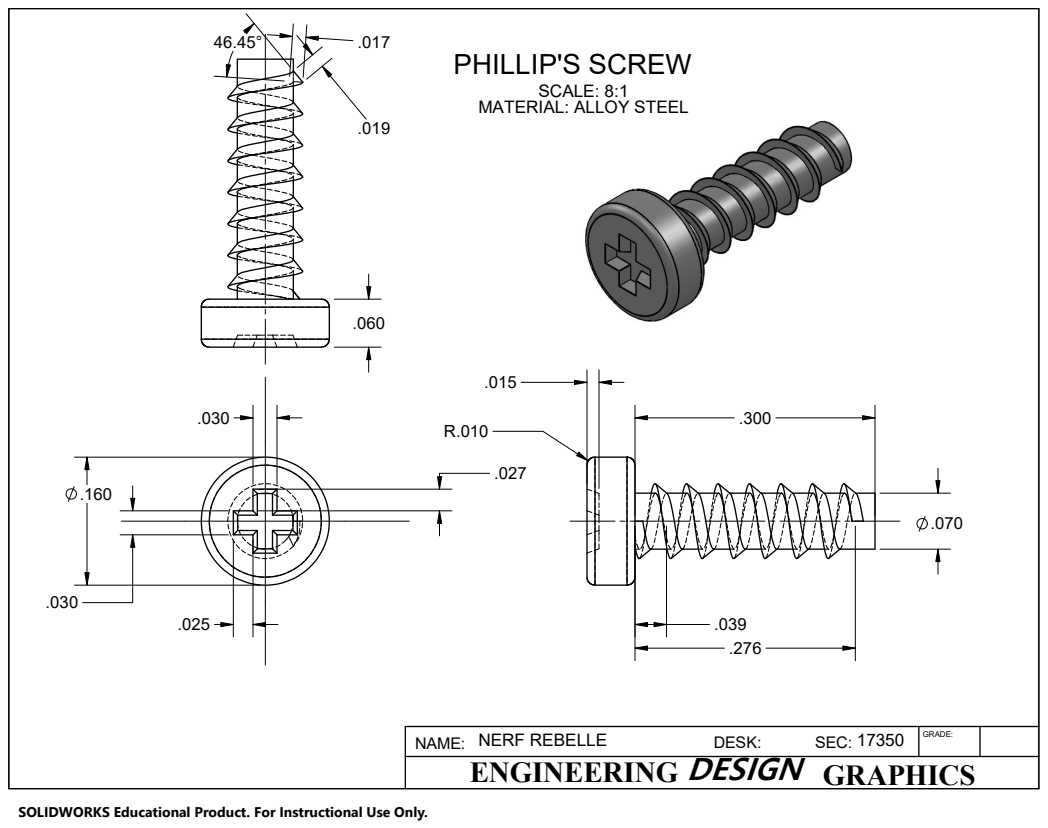
[picture p280: page 1]
NAME:; DESK:; GRADE: SEC:; SCALE: 8:1; NERF REBELLE

MATERIAL: ALLOY STEEL

ENGINEERING DESIGN GRAPHICS

SOLIDWORKS Educational Product. For Instructional Use Only.
