JCam98/me210-engineering-design-graphics/Assignments/Reverse Engineering Project/Drawings/Shaft_Orthogonal_Part_Drawing.pdf

A A

## SHAFT

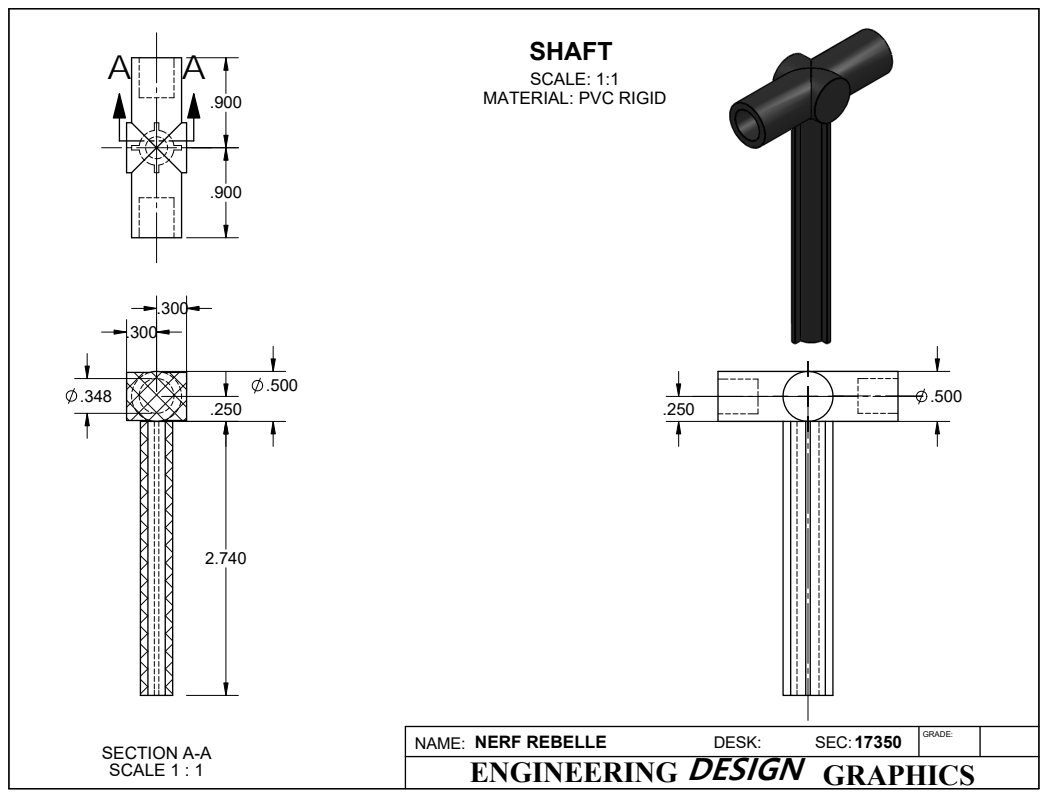
[picture p281: page 1]
GRADE:; D E S I G N ENGINEERING; GRAPHICS; NAME:; DESK:; SEC: SECTION A-A; SCALE 1 : 1; NERF REBELLE

SCALE: 1:1
MATERIAL: PVC RIGID
