JCam98/me210-engineering-design-graphics/Assignments/Reverse Engineering Project/Drawings/TRIGGER_RIVET_ORTHOGONAL.PDF

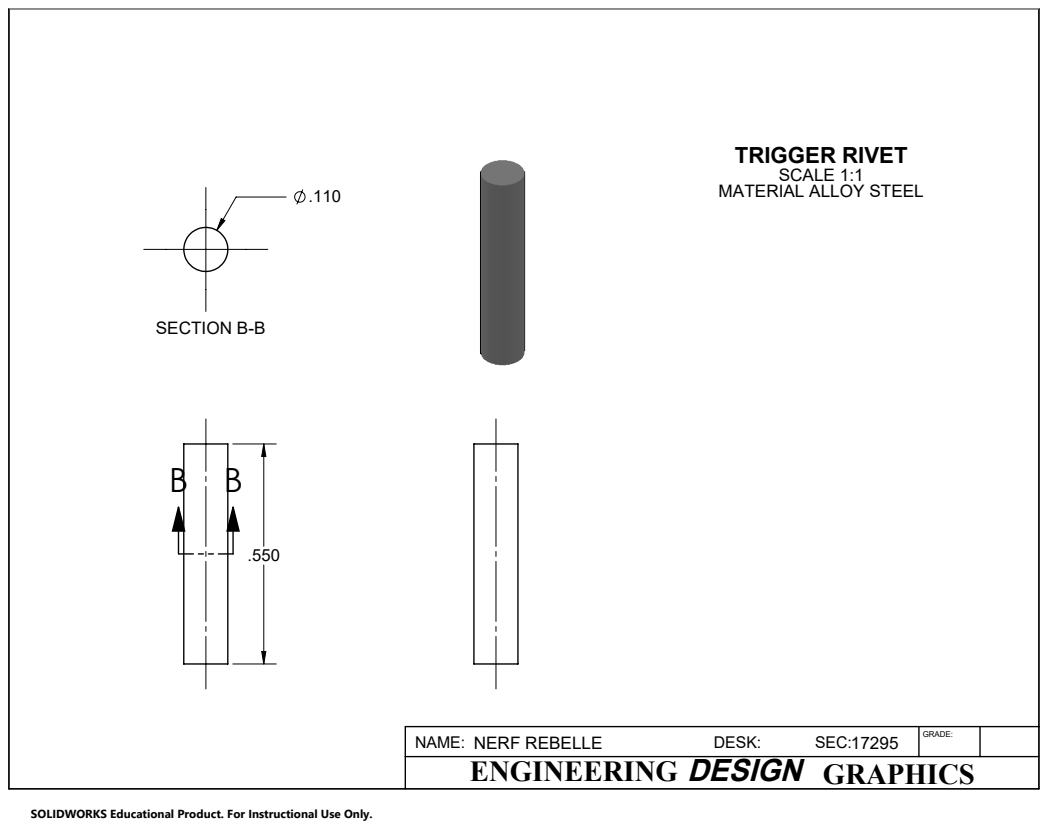
[picture p282: page 1]
SECTION B-B; NERF REBELLE; NAME:; DESK:; GRADE: SEC:

TRIGGER RIVET
SCALE 1:1
MATERIAL ALLOY STEEL

ENGINEERING DESIGN GRAPHICS

SOLIDWORKS Educational Product. For Instructional Use Only.
