JCam98/me210-engineering-design-graphics/Assignments/Reverse Engineering Project/Design Checks/Design_Check_4/PDFS/BASE_PLATE.PDF

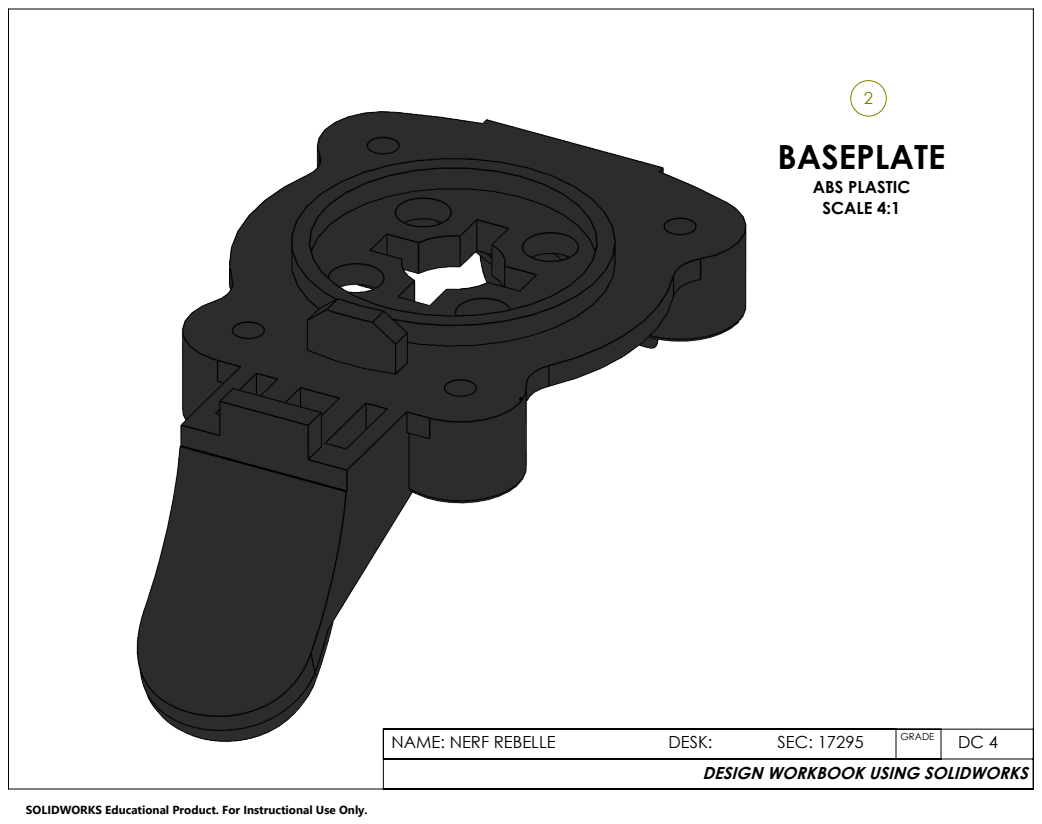
[picture p283: page 1]
ABS PLASTIC SCALE 4:1; NAME: NERF REBELLE; DESK:; SEC: 17295; GRADE

DESIGN WORKBOOK USING SOLIDWORKS

SOLIDWORKS Educational Product. For Instructional Use Only.
